LokiMetaSmith/NASA-COG/docs/references/datasheets/elec/ODECS/README.md

Reference documents for the ODECS.
Date 20231228
Version 1.1 Control and more!

AN_TF800.pdf is the application note on the Power Electronics TF800 series power supply

PowerSupply_SF_HDS800.pdf is the application note on the Power Electronics TF800 series power supply
