LokiMetaSmith/NASA-COG/docs/P_and_ID/Task 6 P_and_ID - Development Configuration rev_7_15_2024.png

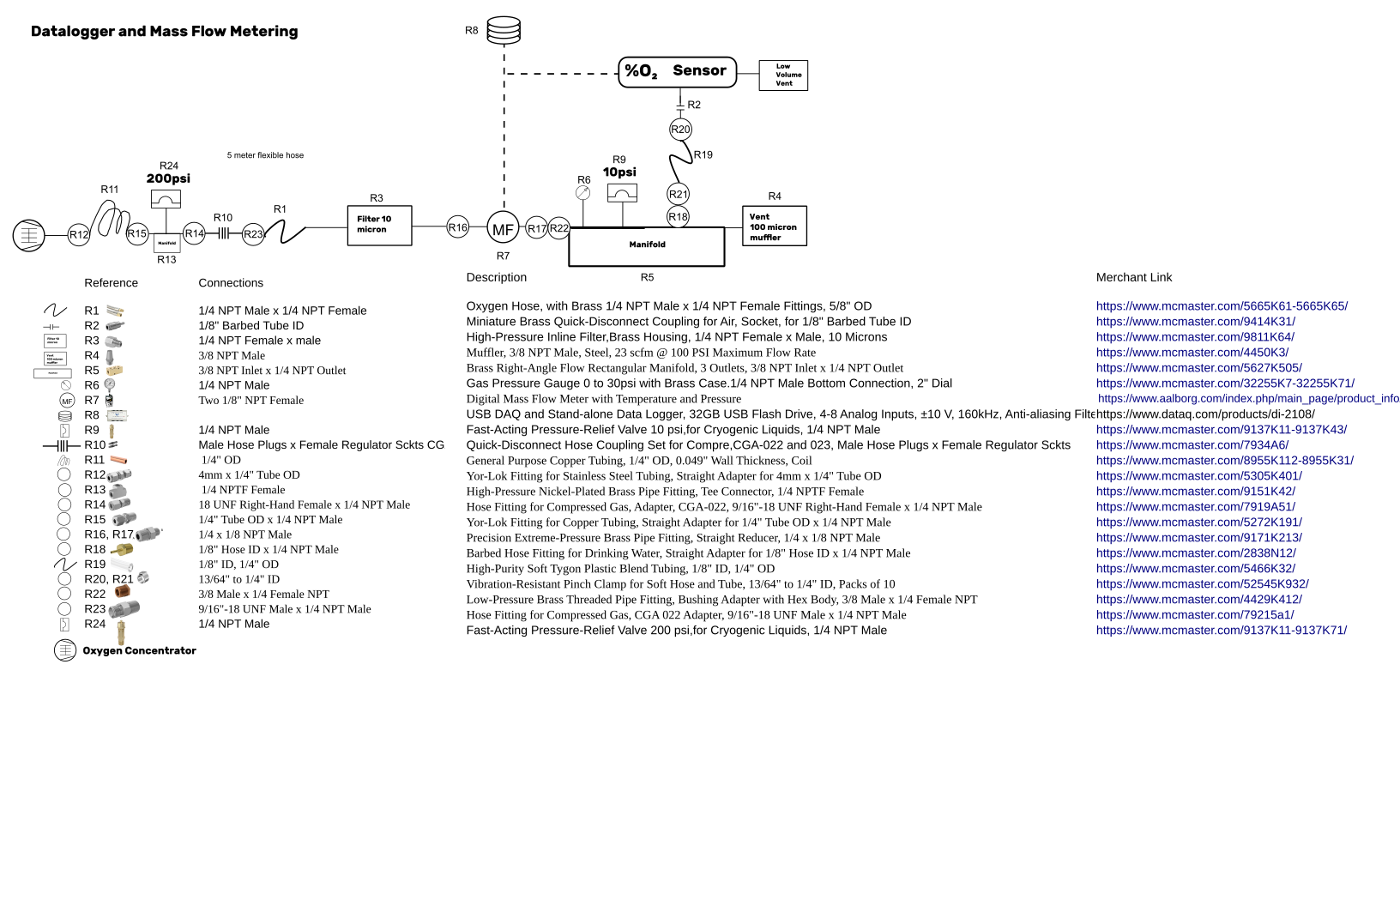
docs/P_and_ID/Task 6 P_and_ID - Development Configuration rev_7_15_2024.png
