LokiMetaSmith/NASA-COG/docs/Task6/Overalll System Diagram.png

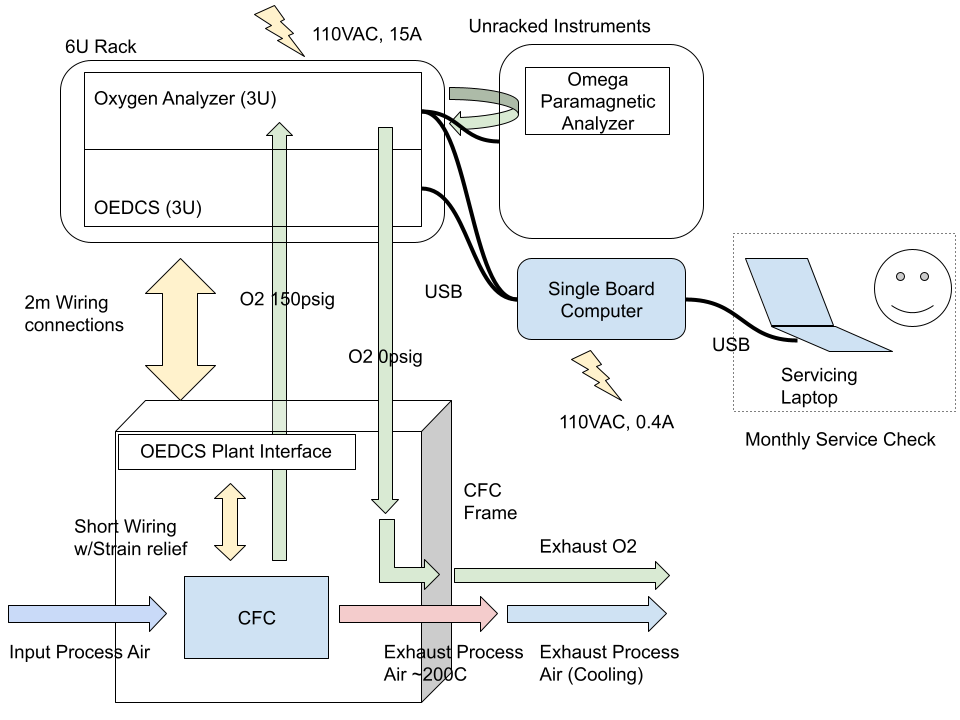
docs/Task6/Overalll System Diagram.png
