LokiMetaSmith/NASA-COG/elec/Control Board/Control_1v1/MountMini12864/20231210_202112.jpg

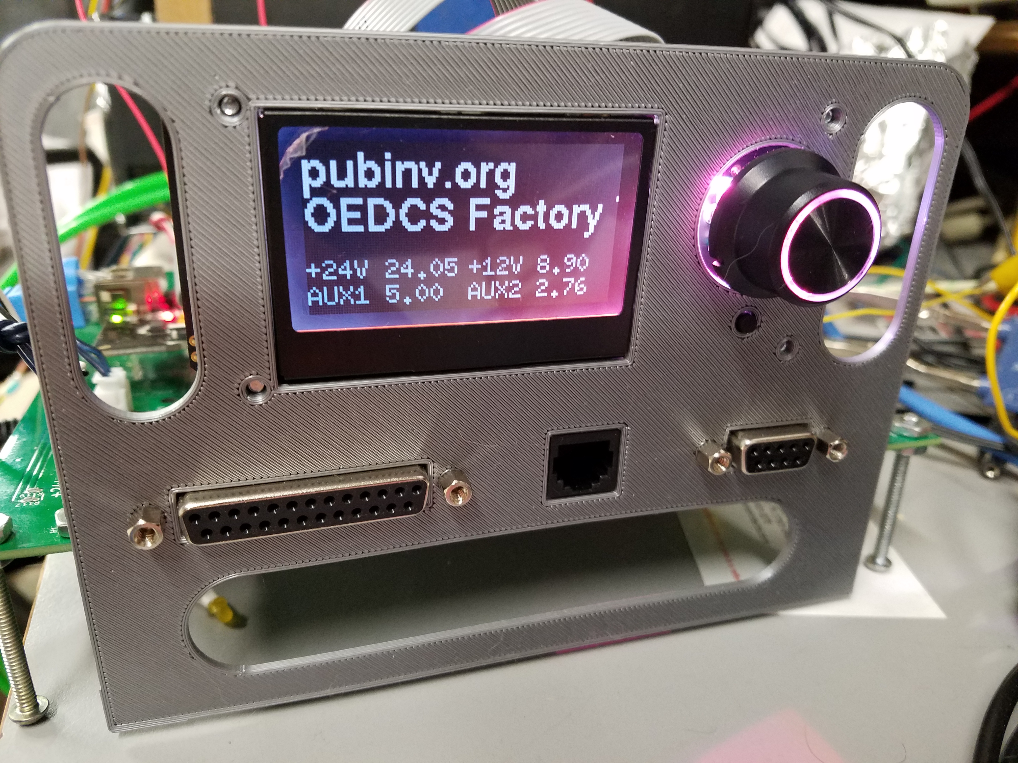
elec/Control Board/Control_1v1/MountMini12864/20231210_202112.jpg
