LokiMetaSmith/NASA-COG/elec/Control Board/Control_1v1/MountMini12864/BIGTREETECHMini12864Connector.png

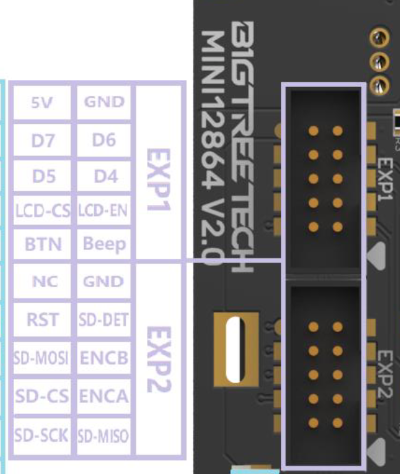
elec/Control Board/Control_1v1/MountMini12864/BIGTREETECHMini12864Connector.png
