LokiMetaSmith/NASA-COG/log-parser/Capture of various analysis views.PNG

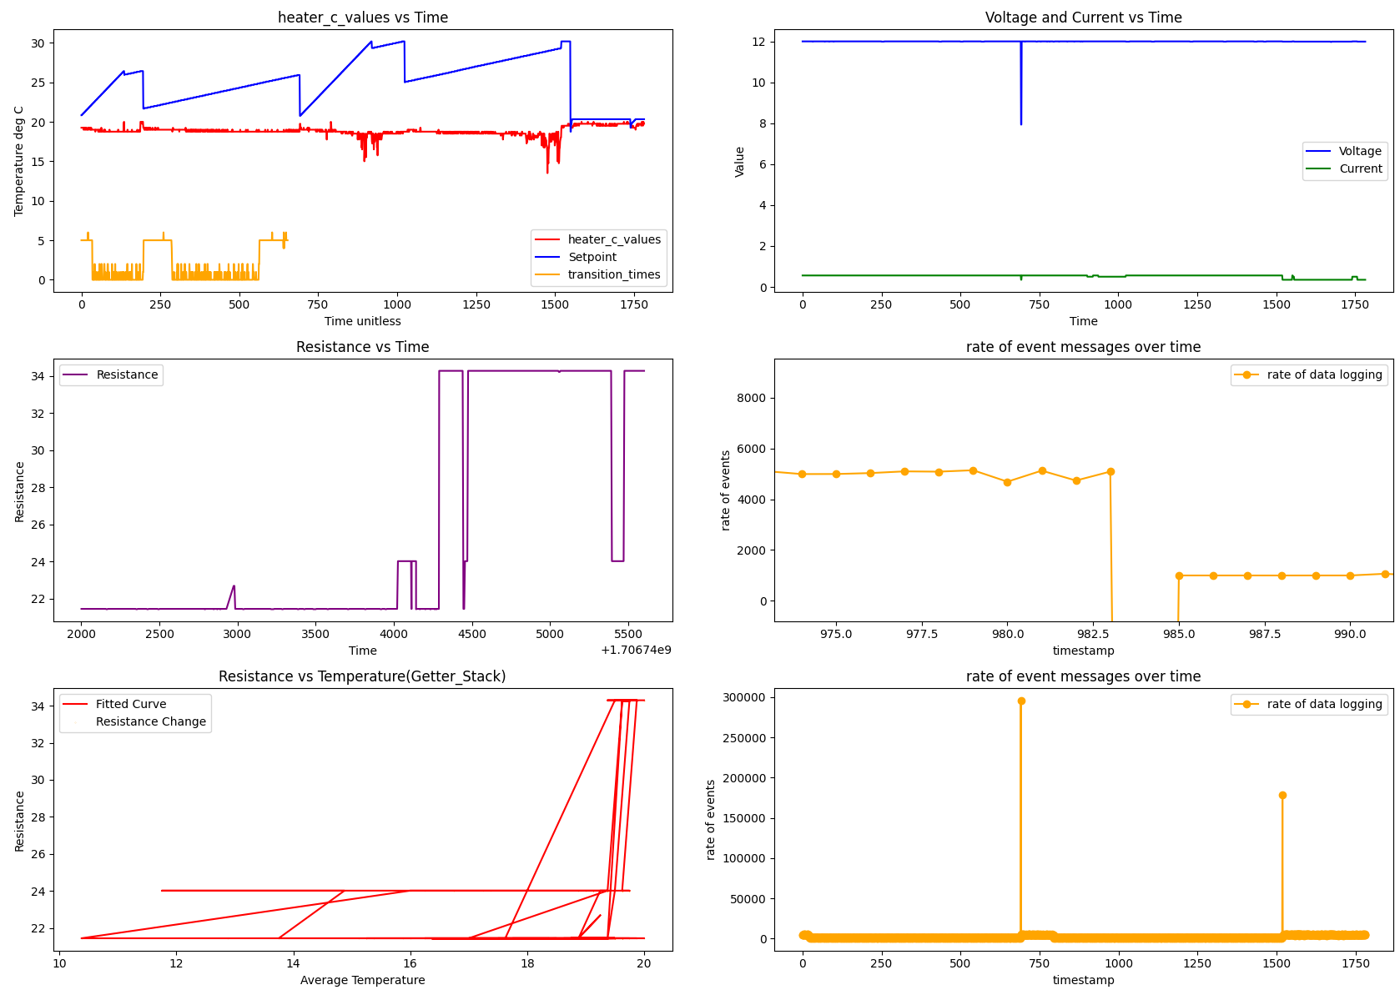
log-parser/Capture of various analysis views.PNG
