LokiMetaSmith/NASA-COG/log-parser/Rate of event messages in milliseconds.PNG

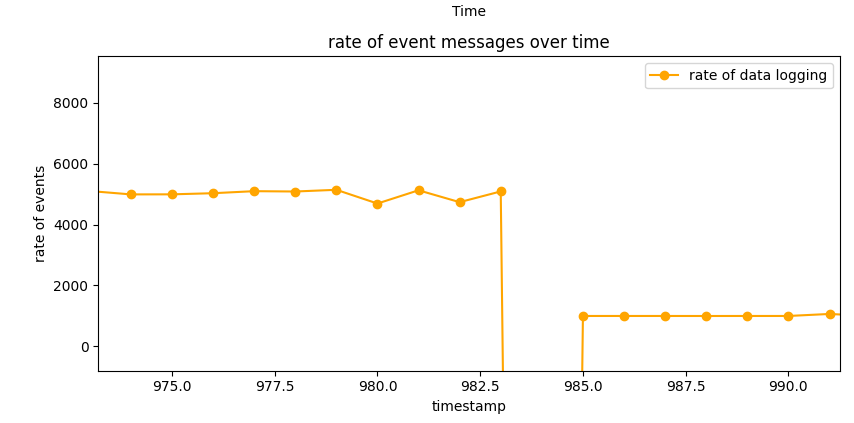
log-parser/Rate of event messages in milliseconds.PNG
