LokiMetaSmith/NASA-COG/elec/Control Board/Control_1v2/PL_Control_1v2_PLandPOS.xls

Sheet: RawImport_PL
Reference | Value | Footprint | Cost | Description | Distributor 1 | Distributor 1 PN | Qty
*_Designator | *_Comment101 | Footprint | 0 | Headers for JLCPCB BOM / PL | JLCPCB | JLCPCB Part # | 1
+3.3V101 | +3.3V | TestPoint:TestPoint_Loop_D2.54mm_Drill1.5mm_Beaded | 0.0696 | Test Points/Test Rings ROHS red | JLCPCB | C5277086 | 1
+5V101 | +5V | TestPoint:TestPoint_Loop_D2.54mm_Drill1.5mm_Beaded | 0.0696 | Test Points/Test Rings ROHS red | JLCPCB | C5277086 | 1
5VHead101 | 5VHead | TestPoint:TestPoint_Loop_D2.54mm_Drill1.5mm_Beaded | 0.0696 | Test Points/Test Rings ROHS red | JLCPCB | C5277086 | 1
C1 | 39pF | Capacitor_SMD:C_0603_1608Metric_Pad1.08x0.95mm_HandSolder | 0.003 | 50V 39pF NP0 Â±5% 0603 Multilayer Ceramic Ca | JLCPCB | C107049 | 1
C2 | 39pF | Capacitor_SMD:C_0603_1608Metric_Pad1.08x0.95mm_HandSolder | 0.003 | 50V 39pF NP0 Â±5% 0603 Multilayer Ceramic Ca | JLCPCB | C107049 | 1
C3 | 39pF | Capacitor_SMD:C_0603_1608Metric_Pad1.08x0.95mm_HandSolder | 0.003 | 50V 39pF NP0 Â±5% 0603 Multilayer Ceramic Ca | JLCPCB | C107049 | 1
C4 | 39pF | Capacitor_SMD:C_0603_1608Metric_Pad1.08x0.95mm_HandSolder | 0.003 | 50V 39pF NP0 Â±5% 0603 Multilayer Ceramic Ca | JLCPCB | C107049 | 1
C5 | 39pF | Capacitor_SMD:C_0603_1608Metric_Pad1.08x0.95mm_HandSolder | 0.003 | 50V 39pF NP0 Â±5% 0603 Multilayer Ceramic Ca | JLCPCB | C107049 | 1
C6 | 39pF | Capacitor_SMD:C_0603_1608Metric_Pad1.08x0.95mm_HandSolder | 0.003 | 50V 39pF NP0 Â±5% 0603 Multilayer Ceramic Ca | JLCPCB | C107049 | 1
C7 | 39pF | Capacitor_SMD:C_0603_1608Metric_Pad1.08x0.95mm_HandSolder | 0.003 | 50V 39pF NP0 Â±5% 0603 Multilayer Ceramic Ca | JLCPCB | C107049 | 1
C8 | 39pF | Capacitor_SMD:C_0603_1608Metric_Pad1.08x0.95mm_HandSolder | 0.003 | 50V 39pF NP0 Â±5% 0603 Multilayer Ceramic Ca | JLCPCB | C107049 | 1
C9 | 39pF | Capacitor_SMD:C_0603_1608Metric_Pad1.08x0.95mm_HandSolder | 0.003 | 50V 39pF NP0 Â±5% 0603 Multilayer Ceramic Ca | JLCPCB | C107049 | 1
C10 | 39pF | Capacitor_SMD:C_0603_1608Metric_Pad1.08x0.95mm_HandSolder | 0.003 | 50V 39pF NP0 Â±5% 0603 Multilayer Ceramic Ca | JLCPCB | C107049 | 1
C11 | 39pF | Capacitor_SMD:C_0603_1608Metric_Pad1.08x0.95mm_HandSolder | 0.003 | 50V 39pF NP0 Â±5% 0603 Multilayer Ceramic Ca | JLCPCB | C107049 | 1
C18 | 1uF | Capacitor_SMD:C_0603_1608Metric_Pad1.08x0.95mm_HandSolder | 0.0037 | 50V 1uF Â±5% 0603 Multilayer Ceramic Ca | JLCPCB | C91183 | 1
C19 | 1uF | Capacitor_SMD:C_0603_1608Metric_Pad1.08x0.95mm_HandSolder | 0.0037 | 50V 1uF Â±5% 0603 Multilayer Ceramic Ca | JLCPCB | C91183 | 1
C20 | 39pF | Capacitor_SMD:C_0603_1608Metric_Pad1.08x0.95mm_HandSolder | 0.003 | 50V 39pF NP0 Â±5% 0603 Multilayer Ceramic Ca | JLCPCB | C107049 | 1
C21 | 39pF | Capacitor_SMD:C_0603_1608Metric_Pad1.08x0.95mm_HandSolder | 0.003 | 50V 39pF NP0 Â±5% 0603 Multilayer Ceramic Ca | JLCPCB | C107049 | 1
C22 | 10nF | Capacitor_SMD:C_0603_1608Metric_Pad1.08x0.95mm_HandSolder | 0.0132 | 50V 10nF NP0 Â±5% 0603 Multilayer Ceramic Capacitors MLCC - SMD/SMT ROHS | JLCPCB | C389113 | 1
C23 | 39pF | Capacitor_SMD:C_0603_1608Metric_Pad1.08x0.95mm_HandSolder | 0.003 | 50V 39pF NP0 Â±5% 0603 Multilayer Ceramic Ca | JLCPCB | C107049 | 1
C24 | 1uF | Capacitor_SMD:C_0603_1608Metric_Pad1.08x0.95mm_HandSolder | 0.0037 | 50V 1uF Â±5% 0603 Multilayer Ceramic Ca | JLCPCB | C91183 | 1
D1 | 5.1V | Diode_SMD:D_MiniMELF | 0.0097 | Â±5% 500mW 5.1V MiniMELF(SOD-80) Zener Diodes ROHS | JLCPCB | C2857227 | 1
D2 | 5.1V | Diode_SMD:D_MiniMELF | 0.0097 | Â±5% 500mW 5.1V MiniMELF(SOD-80) Zener Diodes ROHS | JLCPCB | C2857227 | 1
D3 | 1N5819WS | Diode_SMD:D_SOD-323 | 0.0119 | 40V 600mV@1A 1A SOD-323 Schottky Barrier Diodes (SBD) ROHS | JLCPCB | C191023 | 1
D4 | RED 0603 | LED_SMD:LED_0603_1608Metric_Pad1.05x0.95mm_HandSolder | 0.0054 | LED RED CLEAR SMD | JLCPCB | C2286 | 1
D801 | 1N5819WS | Diode_SMD:D_SOD-323 | 0.0119 | 40V 600mV@1A 1A SOD-323 Schottky Barrier Diodes (SBD) ROHS | JLCPCB | C191023 | 1
D_PSU_RX1 | D_PSU_RX | TestPoint:TestPoint_Loop_D2.54mm_Drill1.5mm_Beaded | 0.0792 | Test Points/Test Rings ROHS black | JLCPCB | C5199807 | 1
D_PSU_RX2 | D_PSU_RX2 | TestPoint:TestPoint_Loop_D2.54mm_Drill1.5mm_Beaded | 0.0792 | Test Points/Test Rings ROHS black | JLCPCB | C5199807 | 1
D_PSU_TX1 | D_PSU_TX | TestPoint:TestPoint_Loop_D2.54mm_Drill1.5mm_Beaded | 0.1865 | Test Points/Test Rings ROHS white | JLCPCB | C5199812 | 1
D_PSU_TX2 | D_PSU_TX2 | TestPoint:TestPoint_Loop_D2.54mm_Drill1.5mm_Beaded | 0.1865 | Test Points/Test Rings ROHS white | JLCPCB | C5199812 | 1
F801 | Polyfuse_0603_1A | Fuse:Fuse_0603_1608Metric | 0.2448 | 6V 1A 50A -40â„ƒ~+85â„ƒ 1.8A 40mÎ© 300ms 120mÎ© 0603 Resettable Fuses ROHS | JLCPCB | C207017 | 1
J1 | DB9_Female_MountingHoles | Connector_Dsub:DSUB-9_Female_Horizontal_P2.77x2.84mm_EdgePinOffset4.94mm_Housed_MountingHolesOffset7.48mm | 0.2718 | 9P Female D-Sub Shrouded 2 3A -50â„ƒ~+105â„ƒ Plugin D-Sub/DVI/HDMI Connectors ROHS | JLCPCB | C141882 | 1
J2 | Conn_01x08 | Connector_PinSocket_2.54mm:PinSocket_1x08_P2.54mm_Vertical | 0.0762 | 2.54mm Plugin 3A 8P -40â„ƒ~+105â„ƒ Straight 1x8P 8.5mm Top Square Holes Plugin,P=2.54mm Female Headers ROHS | JLCPCB | C2905417 | 1
J3 | Conn_01x08 | Connector_PinSocket_2.54mm:PinSocket_1x08_P2.54mm_Vertical | 0.0762 | 2.54mm Plugin 3A 8P -40â„ƒ~+105â„ƒ Straight 1x8P 8.5mm Top Square Holes Plugin,P=2.54mm Female Headers ROHS | JLCPCB | C2905417 | 1
J4 | Conn_01x08 | Connector_PinSocket_2.54mm:PinSocket_1x08_P2.54mm_Vertical | 0.0762 | 2.54mm Plugin 3A 8P -40â„ƒ~+105â„ƒ Straight 1x8P 8.5mm Top Square Holes Plugin,P=2.54mm Female Headers ROHS | JLCPCB | C2905417 | 1
J5 | Conn_01x08 | Connector_PinSocket_2.54mm:PinSocket_1x08_P2.54mm_Vertical | 0.0762 | 2.54mm Plugin 3A 8P -40â„ƒ~+105â„ƒ Straight 1x8P 8.5mm Top Square Holes Plugin,P=2.54mm Female Headers ROHS | JLCPCB | C2905417 | 1
J6 | Conn_01x08 | Connector_PinSocket_2.54mm:PinSocket_1x08_P2.54mm_Vertical | 0.0762 | 2.54mm Plugin 3A 8P -40â„ƒ~+105â„ƒ Straight 1x8P 8.5mm Top Square Holes Plugin,P=2.54mm Female Headers ROHS | JLCPCB | C2905417 | 1
J7 | Conn_01x10 | Connector_PinSocket_2.54mm:PinSocket_1x10_P2.54mm_Vertical | 0.0942 | 2.54mm Plugin 3A 10P -40â„ƒ~+105â„ƒ Straight 1x10P 8.5mm Top Square Holes Plugin,P=2.54mm Female Headers ROHS | JLCPCB | C2905418 | 1
J8 | Conn_02x18_Odd_Even | Connector_PinSocket_2.54mm:PinSocket_2x18_P2.54mm_Vertical | 0.3441 | 2.54mm 2.54mm åŒæŽ’ 36P Straight 2x18P Plugin,P=2.54mm Female Headers ROHS | JLCPCB | C132131 | 1
J9 | Conn_01x10 | Connector_PinSocket_2.54mm:PinSocket_1x10_P2.54mm_Vertical | 0.0942 | 2.54mm Plugin 3A 10P -40â„ƒ~+105â„ƒ Straight 1x10P 8.5mm Top Square Holes Plugin,P=2.54mm Female Headers ROHS | JLCPCB | C2905418 | 1
J10 | Conn_02x12_Odd_Even | PubInv_KiCad_PCB:JST_PHD_B24B-PHDSS_2x12_P2.00mm_Vertical | 1000000 | Conn_02x12_Odd_Even | JLCPCB | C160327 | 1
J11 | Con_01x02_2.5mm | PubInv_KiCad_PCB:JST_XH_B2B-XH-AM_1x02_P2.50mm_Vertical | 0.2156 | 1x2P 2P XH Gold 2 -25â„ƒ~+85â„ƒ 3A 1 2.5mm Brass Direct Insert Plugin,P=2.5mm Wire To Board Connector ROHS | JLCPCB | C265283 | 1
J12 | Con_01x02_2.5mm | PubInv_KiCad_PCB:JST_XH_B2B-XH-AM_1x02_P2.50mm_Vertical | 0.2156 | 1x2P 2P XH Gold 2 -25â„ƒ~+85â„ƒ 3A 1 2.5mm Brass Direct Insert Plugin,P=2.5mm Wire To Board Connector ROHS | JLCPCB | C265283 | 1
J13 | Con_01x02_2.5mm | PubInv_KiCad_PCB:JST_XH_B2B-XH-AM_1x02_P2.50mm_Vertical | 0.2156 | 1x2P 2P XH Gold 2 -25â„ƒ~+85â„ƒ 3A 1 2.5mm Brass Direct Insert Plugin,P=2.5mm Wire To Board Connector ROHS | JLCPCB | C265283 | 1
J14 | Conn_01x10 | Connector_PinSocket_2.54mm:PinSocket_1x10_P2.54mm_Vertical | 0.0942 | 2.54mm Plugin 3A 10P -40â„ƒ~+105â„ƒ Straight 1x10P 8.5mm Top Square Holes Plugin,P=2.54mm Female Headers ROHS | JLCPCB | C2905418 | 1
J15 | DB25_Female_MountingHoles | Connector_Dsub:DSUB-25_Female_Horizontal_P2.77x2.84mm_EdgePinOffset4.94mm_Housed_MountingHolesOffset7.48mm | 0.7217 | 25P Female D-Sub Shrouded 2 3A -50â„ƒ~+105â„ƒ Plugin D-Sub/DVI/HDMI Connectors ROHS | JLCPCB | C190083 | 1
J16 | Conn_01x04 | Connector_PinHeader_2.54mm:PinHeader_1x04_P2.54mm_Vertical | 0.0342 | 2.54mm Plugin 3A 4P -40â„ƒ~+105â„ƒ Straight 1x4P 8.5mm Top Square Holes Plugin,P=2.54mm Female Headers ROHS | JLCPCB | C6332197 | 1
J17 | Conn_01x05 | Connector_PinHeader_2.54mm:PinHeader_1x05_P2.54mm_Vertical | 0.0791 | 2.54mm Plugin 3A 5P -40â„ƒ~+105â„ƒ Straight 1x5P 8.5mm Top Square Holes Plugin,P=2.54mm Female Headers ROHS | JLCPCB | C2897368 | 1
J18 | Conn_01x04 | Connector_PinHeader_2.54mm:PinHeader_1x04_P2.54mm_Vertical | 0.0342 | 2.54mm Plugin 3A 4P -40â„ƒ~+105â„ƒ Straight 1x4P 8.5mm Top Square Holes Plugin,P=2.54mm Female Headers ROHS | JLCPCB | C6332197 | 1
J19 | Conn_01x07 | Connector_PinHeader_2.54mm:PinHeader_1x07_P2.54mm_Vertical | 0.0543 | 2.54mm Plugin 3A 7P -40â„ƒ~+105â„ƒ Straight 1x7P 8.5mm Top Square Holes Plugin,P=2.54mm Female Headers ROHS | JLCPCB | C2932672 | 1
J23 | Con_01x02_0.1" | Connector_PinHeader_2.54mm:PinHeader_1x02_P2.54mm_Vertical | 0.0115 | Direct Insert Policy 2.5mm 2P 6mm -40â„ƒ~+105â„ƒ 3mm 2.54mm Single Row Black Brass 1x2P Plugin,P=2.54mm Pin Headers ROHS | JLCPCB | C492401 | 1
J24 | Conn_01x04 | Connector_PinHeader_2.54mm:PinHeader_1x04_P2.54mm_Vertical | 0.0342 | 2.54mm Plugin 3A 4P -40â„ƒ~+105â„ƒ Straight 1x4P 8.5mm Top Square Holes Plugin,P=2.54mm Female Headers ROHS | JLCPCB | C6332197 | 1
J25 | Con_01x02_2.5mm | PubInv_KiCad_PCB:JST_XH_B2B-XH-AM_1x02_P2.50mm_Vertical | 0.2156 | 1x2P 2P XH Gold 2 -25â„ƒ~+85â„ƒ 3A 1 2.5mm Brass Direct Insert Plugin,P=2.5mm Wire To Board Connector ROHS | JLCPCB | C265283 | 1
J26 | Conn_01x10 | Connector_PinSocket_2.54mm:PinSocket_1x10_P2.54mm_Vertical | 0.0942 | 2.54mm Plugin 3A 10P -40â„ƒ~+105â„ƒ Straight 1x10P 8.5mm Top Square Holes Plugin,P=2.54mm Female Headers ROHS | JLCPCB | C2905418 | 1
J27 | Conn_02x12_Odd_Even | PubInv_KiCad_PCB:JST_PHD_B24B-PHDSS_2x12_P2.00mm_Vertical | 1000000 | Conn_02x12_Odd_Even | JLCPCB | C160327 | 1
J28 | Con_01x02_2.5mm | PubInv_KiCad_PCB:JST_XH_B2B-XH-AM_1x02_P2.50mm_Vertical | 0.2156 | 1x2P 2P XH Gold 2 -25â„ƒ~+85â„ƒ 3A 1 2.5mm Brass Direct Insert Plugin,P=2.5mm Wire To Board Connector ROHS | JLCPCB | C265283 | 1
J29 | Conn_01x10 | Connector_PinSocket_2.54mm:PinSocket_1x10_P2.54mm_Vertical | 0.0942 | 2.54mm Plugin 3A 10P -40â„ƒ~+105â„ƒ Straight 1x10P 8.5mm Top Square Holes Plugin,P=2.54mm Female Headers ROHS | JLCPCB | C2905418 | 1
J30 | Con_01x02_2.5mm | PubInv_KiCad_PCB:JST_XH_B2B-XH-AM_1x02_P2.50mm_Vertical | 0.2156 | 1x2P 2P XH Gold 2 -25â„ƒ~+85â„ƒ 3A 1 2.5mm Brass Direct Insert Plugin,P=2.5mm Wire To Board Connector ROHS | JLCPCB | C265283 | 1
J31 | Con_01x02_2.5mm | PubInv_KiCad_PCB:JST_XH_B2B-XH-AM_1x02_P2.50mm_Vertical | 0.2156 | 1x2P 2P XH Gold 2 -25â„ƒ~+85â„ƒ 3A 1 2.5mm Brass Direct Insert Plugin,P=2.5mm Wire To Board Connector ROHS | JLCPCB | C265283 | 1
J32 | Con_01x02_2.5mm | PubInv_KiCad_PCB:JST_XH_B2B-XH-AM_1x02_P2.50mm_Vertical | 0.2156 | 1x2P 2P XH Gold 2 -25â„ƒ~+85â„ƒ 3A 1 2.5mm Brass Direct Insert Plugin,P=2.5mm Wire To Board Connector ROHS | JLCPCB | C265283 | 1
J33 | Con_01x02_2.5mm | PubInv_KiCad_PCB:JST_XH_B2B-XH-AM_1x02_P2.50mm_Vertical | 0.2156 | 1x2P 2P XH Gold 2 -25â„ƒ~+85â„ƒ 3A 1 2.5mm Brass Direct Insert Plugin,P=2.5mm Wire To Board Connector ROHS | JLCPCB | C265283 | 1
J34 | Con_01x02_2.5mm | PubInv_KiCad_PCB:JST_XH_B2B-XH-AM_1x02_P2.50mm_Vertical | 0.2156 | 1x2P 2P XH Gold 2 -25â„ƒ~+85â„ƒ 3A 1 2.5mm Brass Direct Insert Plugin,P=2.5mm Wire To Board Connector ROHS | JLCPCB | C265283 | 1
J35 | Conn_02x05_Odd_Even | Connector_IDC:IDC-Header_2x05_P2.54mm_Vertical | 0.48 | 2.54mm Box 10Pin Male Straight | JLCPCB | C5665 | 1
J36 | Conn_02x05_Odd_Even | Connector_IDC:IDC-Header_2x05_P2.54mm_Vertical | 0.48 | 2.54mm Box 10Pin Male Straight | JLCPCB | C5665 | 1
J37 | Conn_01x04 | Connector_PinHeader_2.54mm:PinHeader_1x04_P2.54mm_Vertical | 0.0342 | 2.54mm Plugin 3A 4P -40â„ƒ~+105â„ƒ Straight 1x4P 8.5mm Top Square Holes Plugin,P=2.54mm Female Headers ROHS | JLCPCB | C6332197 | 1
J101 | Con_01x02_2.5mm | PubInv_KiCad_PCB:JST_XH_B2B-XH-AM_1x02_P2.50mm_Vertical | 0.2156 | 1x2P 2P XH Gold 2 -25â„ƒ~+85â„ƒ 3A 1 2.5mm Brass Direct Insert Plugin,P=2.5mm Wire To Board Connector ROHS | JLCPCB | C265283 | 1
J201 | Con_01x02_2.5mm | PubInv_KiCad_PCB:JST_XH_B2B-XH-AM_1x02_P2.50mm_Vertical | 0.2156 | 1x2P 2P XH Gold 2 -25â„ƒ~+85â„ƒ 3A 1 2.5mm Brass Direct Insert Plugin,P=2.5mm Wire To Board Connector ROHS | JLCPCB | C265283 | 1
J801 | Conn_01x03_0.1" | Connector_PinHeader_2.54mm:PinHeader_1x03_P2.54mm_Vertical | 0.0141 | Gold 250V 3A Direct Insert Policy 2.54mm 3P 260â„ƒ 6mm -40â„ƒ~+105â„ƒ 3mm 2.54mm Brass Black Single Row 2.54mm 1x3P Plugin,P=2.54mm Pin Headers ROHS | JLCPCB | C6332196 | 1
J802 | Con_01x02_0.1" | Connector_PinHeader_2.54mm:PinHeader_1x02_P2.54mm_Vertical | 0.0115 | Direct Insert Policy 2.5mm 2P 6mm -40â„ƒ~+105â„ƒ 3mm 2.54mm Single Row Black Brass 1x2P Plugin,P=2.54mm Pin Headers ROHS | JLCPCB | C492401 | 1
J804 | Screw_Terminal_01x02_5.08mm | TerminalBlock_Phoenix:TerminalBlock_Phoenix_MKDS-1,5-2-5.08_1x02_P5.08mm_Horizontal | 0.1551 | Screw_Terminal_01x02_5.08mm | JLCPCB | C5142622 | 1
J805 | Con_01x02_0.1" | Connector_PinHeader_2.54mm:PinHeader_1x02_P2.54mm_Vertical | 0.0115 | Direct Insert Policy 2.5mm 2P 6mm -40â„ƒ~+105â„ƒ 3mm 2.54mm Single Row Black Brass 1x2P Plugin,P=2.54mm Pin Headers ROHS | JLCPCB | C492401 | 1
JP9 | MAX31850K | PubInv_KiCad_PCB:Adafruit_MAX31850K_Module | 14.95 | 2.54mm Plugin 3A 8P -40â„ƒ~+105â„ƒ Straight 1x8P 8.5mm Top Square Holes Plugin,P=2.54mm Female Headers ROHS | JLCPCB | C2905417 | 1
JP10 | MAX31850K | PubInv_KiCad_PCB:Adafruit_MAX31850K_Module | 14.95 | 2.54mm Plugin 3A 8P -40â„ƒ~+105â„ƒ Straight 1x8P 8.5mm Top Square Holes Plugin,P=2.54mm Female Headers ROHS | JLCPCB | C2905417 | 1
JP15 | MAX31850K | PubInv_KiCad_PCB:Adafruit_MAX31850K_Module | 14.95 | 2.54mm Plugin 3A 8P -40â„ƒ~+105â„ƒ Straight 1x8P 8.5mm Top Square Holes Plugin,P=2.54mm Female Headers ROHS | JLCPCB | C2905417 | 1
JP16 | MAX31855 | PubInv_KiCad_PCB:Adafruit_MAX31855_Module | 14.95 | 2.54mm Plugin 3A 6P -40â„ƒ~+105â„ƒ Straight 1x6P 8.5mm Top Square Holes Plugin,P=2.54mm Female Headers ROHS | JLCPCB | C2905416 | 1
JP17 | MAX31855 | PubInv_KiCad_PCB:Adafruit_MAX31855_Module | 14.95 | 2.54mm Plugin 3A 6P -40â„ƒ~+105â„ƒ Straight 1x6P 8.5mm Top Square Holes Plugin,P=2.54mm Female Headers ROHS | JLCPCB | C2905416 | 1
JP18 | MAX31855 | PubInv_KiCad_PCB:Adafruit_MAX31855_Module | 14.95 | 2.54mm Plugin 3A 6P -40â„ƒ~+105â„ƒ Straight 1x6P 8.5mm Top Square Holes Plugin,P=2.54mm Female Headers ROHS | JLCPCB | C2905416 | 1
JP19 | MCP9600 | PubInv_KiCad_PCB:Adafruit_MCP9600_Module | 15.95 | 2.54mm Plugin 3A 9P -40â„ƒ~+105â„ƒ Straight 1x9P 8.5mm Top Square Holes Plugin,P=2.54mm Female Headers ROHS | JLCPCB | C2932673 | 1
JP20 | MCP9600 | PubInv_KiCad_PCB:Adafruit_MCP9600_Module | 15.95 | 2.54mm Plugin 3A 9P -40â„ƒ~+105â„ƒ Straight 1x9P 8.5mm Top Square Holes Plugin,P=2.54mm Female Headers ROHS | JLCPCB | C2932673 | 1
JP21 | MCP9600 | PubInv_KiCad_PCB:Adafruit_MCP9600_Module | 15.95 | 2.54mm Plugin 3A 9P -40â„ƒ~+105â„ƒ Straight 1x9P 8.5mm Top Square Holes Plugin,P=2.54mm Female Headers ROHS | JLCPCB | C2932673 | 1
JP205 | MAX31850K | PubInv_KiCad_PCB:Adafruit_MAX31850K_Module | 14.95 | 2.54mm Plugin 3A 8P -40â„ƒ~+105â„ƒ Straight 1x8P 8.5mm Top Square Holes Plugin,P=2.54mm Female Headers ROHS | JLCPCB | C2905417 | 1
K801 | Relay SRU-12VDC | Relay_THT:Relay_SPDT_Omron-G5LE-1 | 0.4224 | Relay SRU-12VDC-SL-C | JLCPCB | C47402 | 1
Q1 | BSS138 | Package_TO_SOT_SMD:SOT-23 | 0.0196 | 50V 220mA 3.5Î©@10V,220mA 360mW 1.5V@1mA N Channel SOT-23 MOSFETs ROHS | JLCPCB | C400505 | 1
Q2 | NCE01P30K | Package_TO_SOT_SMD:TO-252-2 | $0.51 | P Channel -100V 30A(Tc) 2.5V @ 250uA 58mÎ© @ 15A,10V 120W(Tc) TO-252-2L MOSFET RoHS | JLCPCB | C115991 | 1
Q3 | BSS138 | Package_TO_SOT_SMD:SOT-23 | 0.0196 | 50V 220mA 3.5Î©@10V,220mA 360mW 1.5V@1mA N Channel SOT-23 MOSFETs ROHS | JLCPCB | C400505 | 1
Q4 | BSS138 | Package_TO_SOT_SMD:SOT-23 | 0.0196 | 50V 220mA 3.5Î©@10V,220mA 360mW 1.5V@1mA N Channel SOT-23 MOSFETs ROHS | JLCPCB | C400505 | 1
Q9 | BSS138 | Package_TO_SOT_SMD:SOT-23 | 0.0196 | 50V 220mA 3.5Î©@10V,220mA 360mW 1.5V@1mA N Channel SOT-23 MOSFETs ROHS | JLCPCB | C400505 | 1
Q10 | BSS138 | Package_TO_SOT_SMD:SOT-23 | 0.0196 | 50V 220mA 3.5Î©@10V,220mA 360mW 1.5V@1mA N Channel SOT-23 MOSFETs ROHS | JLCPCB | C400505 | 1
Q11 | BSS138 | Package_TO_SOT_SMD:SOT-23 | 0.0196 | 50V 220mA 3.5Î©@10V,220mA 360mW 1.5V@1mA N Channel SOT-23 MOSFETs ROHS | JLCPCB | C400505 | 1
Q12 | BSS138 | Package_TO_SOT_SMD:SOT-23 | 0.0196 | 50V 220mA 3.5Î©@10V,220mA 360mW 1.5V@1mA N Channel SOT-23 MOSFETs ROHS | JLCPCB | C400505 | 1
Q13 | BSS138 | Package_TO_SOT_SMD:SOT-23 | 0.0196 | 50V 220mA 3.5Î©@10V,220mA 360mW 1.5V@1mA N Channel SOT-23 MOSFETs ROHS | JLCPCB | C400505 | 1
Q14 | BSS138 | Package_TO_SOT_SMD:SOT-23 | 0.0196 | 50V 220mA 3.5Î©@10V,220mA 360mW 1.5V@1mA N Channel SOT-23 MOSFETs ROHS | JLCPCB | C400505 | 1
Q801 | BSS138 | Package_TO_SOT_SMD:SOT-23 | 0.0196 | 50V 220mA 3.5Î©@10V,220mA 360mW 1.5V@1mA N Channel SOT-23 MOSFETs ROHS | JLCPCB | C400505 | 1
R1 | 1R0 | Resistor_SMD:R_0603_1608Metric_Pad0.98x0.95mm_HandSolder | 0.0015 | 0.1W Â±5% 1Î© 0603 Chip Resistor - Surface Mount ROHS | JLCPCB | C269434 | 1
R2 | 1R0 | Resistor_SMD:R_0603_1608Metric_Pad0.98x0.95mm_HandSolder | 0.0015 | 0.1W Â±5% 1Î© 0603 Chip Resistor - Surface Mount ROHS | JLCPCB | C269434 | 1
R3 | 1R0 | Resistor_SMD:R_0603_1608Metric_Pad0.98x0.95mm_HandSolder | 0.0015 | 0.1W Â±5% 1Î© 0603 Chip Resistor - Surface Mount ROHS | JLCPCB | C269434 | 1
R4 | 1R0 | Resistor_SMD:R_0603_1608Metric_Pad0.98x0.95mm_HandSolder | 0.0015 | 0.1W Â±5% 1Î© 0603 Chip Resistor - Surface Mount ROHS | JLCPCB | C269434 | 1
R5 | 1R0 | Resistor_SMD:R_0603_1608Metric_Pad0.98x0.95mm_HandSolder | 0.0015 | 0.1W Â±5% 1Î© 0603 Chip Resistor - Surface Mount ROHS | JLCPCB | C269434 | 1
R6 | 1R0 | Resistor_SMD:R_0603_1608Metric_Pad0.98x0.95mm_HandSolder | 0.0015 | 0.1W Â±5% 1Î© 0603 Chip Resistor - Surface Mount ROHS | JLCPCB | C269434 | 1
R7 | 1R0 | Resistor_SMD:R_0603_1608Metric_Pad0.98x0.95mm_HandSolder | 0.0015 | 0.1W Â±5% 1Î© 0603 Chip Resistor - Surface Mount ROHS | JLCPCB | C269434 | 1
R8 | 1R0 | Resistor_SMD:R_0603_1608Metric_Pad0.98x0.95mm_HandSolder | 0.0015 | 0.1W Â±5% 1Î© 0603 Chip Resistor - Surface Mount ROHS | JLCPCB | C269434 | 1
R9 | 1R0 | Resistor_SMD:R_0603_1608Metric_Pad0.98x0.95mm_HandSolder | 0.0015 | 0.1W Â±5% 1Î© 0603 Chip Resistor - Surface Mount ROHS | JLCPCB | C269434 | 1
R10 | 1R0 | Resistor_SMD:R_0603_1608Metric_Pad0.98x0.95mm_HandSolder | 0.0015 | 0.1W Â±5% 1Î© 0603 Chip Resistor - Surface Mount ROHS | JLCPCB | C269434 | 1
R11 | 1R0 | Resistor_SMD:R_0603_1608Metric_Pad0.98x0.95mm_HandSolder | 0.0015 | 0.1W Â±5% 1Î© 0603 Chip Resistor - Surface Mount ROHS | JLCPCB | C269434 | 1
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
R81 | 10K | Resistor_SMD:R_0603_1608Metric_Pad0.98x0.95mm_HandSolder | 0.0015 | 100mW Â±1% 10kÎ© 0603 Chip Resistor - Surface Mount ROHS | JLCPCB | C269701 | 1
R82 | 1R0 | Resistor_SMD:R_0603_1608Metric_Pad0.98x0.95mm_HandSolder | 0.0015 | 0.1W Â±5% 1Î© 0603 Chip Resistor - Surface Mount ROHS | JLCPCB | C269434 | 1
R83 | 4K7 | Resistor_SMD:R_0603_1608Metric_Pad0.98x0.95mm_HandSolder | 0.0015 | 100mW Thick Film Resistors Â±100ppm/â„ƒ Â±1% 4.7kÎ© 0603 Chip Resistor - Surface Mount ROHS | JLCPCB | C23162 | 1
R84 | 1R0 | Resistor_SMD:R_0603_1608Metric_Pad0.98x0.95mm_HandSolder | 0.0015 | 0.1W Â±5% 1Î© 0603 Chip Resistor - Surface Mount ROHS | JLCPCB | C269434 | 1
R88 | 1R0 | Resistor_SMD:R_0603_1608Metric_Pad0.98x0.95mm_HandSolder | 0.0015 | 0.1W Â±5% 1Î© 0603 Chip Resistor - Surface Mount ROHS | JLCPCB | C269434 | 1
R91 | 1R0 | Resistor_SMD:R_0603_1608Metric_Pad0.98x0.95mm_HandSolder | 0.0015 | 0.1W Â±5% 1Î© 0603 Chip Resistor - Surface Mount ROHS | JLCPCB | C269434 | 1
R92 | 1R0 | Resistor_SMD:R_0603_1608Metric_Pad0.98x0.95mm_HandSolder | 0.0015 | 0.1W Â±5% 1Î© 0603 Chip Resistor - Surface Mount ROHS | JLCPCB | C269434 | 1
R97 | 1R0 | Resistor_SMD:R_0603_1608Metric_Pad0.98x0.95mm_HandSolder | 0.0015 | 0.1W Â±5% 1Î© 0603 Chip Resistor - Surface Mount ROHS | JLCPCB | C269434 | 1
R98 | 1R0 | Resistor_SMD:R_0603_1608Metric_Pad0.98x0.95mm_HandSolder | 0.0015 | 0.1W Â±5% 1Î© 0603 Chip Resistor - Surface Mount ROHS | JLCPCB | C269434 | 1
R99 | 1R0 | Resistor_SMD:R_0603_1608Metric_Pad0.98x0.95mm_HandSolder | 0.0015 | 0.1W Â±5% 1Î© 0603 Chip Resistor - Surface Mount ROHS | JLCPCB | C269434 | 1
R100 | 1K | Resistor_SMD:R_0603_1608Metric_Pad0.98x0.95mm_HandSolder | 0.0015 | 0.1W Â±1% 1kÎ© 0603 Chip Resistor - Surface Mount ROHS | JLCPCB | C269704 | 1
R101 | 10K | Resistor_SMD:R_0603_1608Metric_Pad0.98x0.95mm_HandSolder | 0.0015 | 100mW Â±1% 10kÎ© 0603 Chip Resistor - Surface Mount ROHS | JLCPCB | C269701 | 1
R102 | 4K7 | Resistor_SMD:R_0603_1608Metric_Pad0.98x0.95mm_HandSolder | 0.0015 | 100mW Thick Film Resistors Â±100ppm/â„ƒ Â±1% 4.7kÎ© 0603 Chip Resistor - Surface Mount ROHS | JLCPCB | C23162 | 1
R103 | 10K | Resistor_SMD:R_0603_1608Metric_Pad0.98x0.95mm_HandSolder | 0.0015 | 100mW Â±1% 10kÎ© 0603 Chip Resistor - Surface Mount ROHS | JLCPCB | C269701 | 1
R104 | 10K | Resistor_SMD:R_0603_1608Metric_Pad0.98x0.95mm_HandSolder | 0.0015 | 100mW Â±1% 10kÎ© 0603 Chip Resistor - Surface Mount ROHS | JLCPCB | C269701 | 1
R105 | 10K | Resistor_SMD:R_0603_1608Metric_Pad0.98x0.95mm_HandSolder | 0.0015 | 100mW Â±1% 10kÎ© 0603 Chip Resistor - Surface Mount ROHS | JLCPCB | C269701 | 1
R106 | 20K | Resistor_SMD:R_0603_1608Metric_Pad0.98x0.95mm_HandSolder | 0.0008 | 100mW Thick Film Resistors 75V Â±100ppm/â„ƒ Â±1% 10kÎ© 0603 Chip Resistor - Surface Mount ROHS | JLCPCB | C25804 | 1
R107 | 10K | Resistor_SMD:R_0603_1608Metric_Pad0.98x0.95mm_HandSolder | 0.0015 | 100mW Â±1% 10kÎ© 0603 Chip Resistor - Surface Mount ROHS | JLCPCB | C269701 | 1
R108 | 20K | Resistor_SMD:R_0603_1608Metric_Pad0.98x0.95mm_HandSolder | 0.0008 | 100mW Thick Film Resistors 75V Â±100ppm/â„ƒ Â±1% 10kÎ© 0603 Chip Resistor - Surface Mount ROHS | JLCPCB | C25804 | 1
R109 | 1R0 | Resistor_SMD:R_0603_1608Metric_Pad0.98x0.95mm_HandSolder | 0.0015 | 0.1W Â±5% 1Î© 0603 Chip Resistor - Surface Mount ROHS | JLCPCB | C269434 | 1
R110 | 1R0 | Resistor_SMD:R_0603_1608Metric_Pad0.98x0.95mm_HandSolder | 0.0015 | 0.1W Â±5% 1Î© 0603 Chip Resistor - Surface Mount ROHS | JLCPCB | C269434 | 1
R111 | 1R0 | Resistor_SMD:R_0603_1608Metric_Pad0.98x0.95mm_HandSolder | 0.0015 | 0.1W Â±5% 1Î© 0603 Chip Resistor - Surface Mount ROHS | JLCPCB | C269434 | 1
R112 | 1R0 | Resistor_SMD:R_0603_1608Metric_Pad0.98x0.95mm_HandSolder | 0.0015 | 0.1W Â±5% 1Î© 0603 Chip Resistor - Surface Mount ROHS | JLCPCB | C269434 | 1
R113 | 10K | Resistor_SMD:R_0603_1608Metric_Pad0.98x0.95mm_HandSolder | 0.0015 | 100mW Â±1% 10kÎ© 0603 Chip Resistor - Surface Mount ROHS | JLCPCB | C269701 | 1
R114 | 10K | Resistor_SMD:R_0603_1608Metric_Pad0.98x0.95mm_HandSolder | 0.0015 | 100mW Â±1% 10kÎ© 0603 Chip Resistor - Surface Mount ROHS | JLCPCB | C269701 | 1
R115 | 1K | Resistor_SMD:R_0603_1608Metric_Pad0.98x0.95mm_HandSolder | 0.0015 | 0.1W Â±1% 1kÎ© 0603 Chip Resistor - Surface Mount ROHS | JLCPCB | C269704 | 1
R116 | 1K | Resistor_SMD:R_0603_1608Metric_Pad0.98x0.95mm_HandSolder | 0.0015 | 0.1W Â±1% 1kÎ© 0603 Chip Resistor - Surface Mount ROHS | JLCPCB | C269704 | 1
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
R181 | 4K7 | Resistor_SMD:R_0603_1608Metric_Pad0.98x0.95mm_HandSolder | 0.0015 | 100mW Thick Film Resistors Â±100ppm/â„ƒ Â±1% 4.7kÎ© 0603 Chip Resistor - Surface Mount ROHS | JLCPCB | C23162 | 1
R182 | 10K | Resistor_SMD:R_0603_1608Metric_Pad0.98x0.95mm_HandSolder | 0.0015 | 100mW Â±1% 10kÎ© 0603 Chip Resistor - Surface Mount ROHS | JLCPCB | C269701 | 1
R183 | 10K | Resistor_SMD:R_0603_1608Metric_Pad0.98x0.95mm_HandSolder | 0.0015 | 100mW Â±1% 10kÎ© 0603 Chip Resistor - Surface Mount ROHS | JLCPCB | C269701 | 1
R184 | 2K | Resistor_SMD:R_0603_1608Metric_Pad0.98x0.95mm_HandSolder | 0.0015 | 100mW Â±1% 2kÎ© 0603 Chip Resistor - Surface Mount ROHS | JLCPCB | C269421 | 1
R185 | 2K | Resistor_SMD:R_0603_1608Metric_Pad0.98x0.95mm_HandSolder | 0.0015 | 100mW Â±1% 2kÎ© 0603 Chip Resistor - Surface Mount ROHS | JLCPCB | C269421 | 1
R201 | 1K | Resistor_SMD:R_0603_1608Metric_Pad0.98x0.95mm_HandSolder | 0.0015 | 0.1W Â±1% 1kÎ© 0603 Chip Resistor - Surface Mount ROHS | JLCPCB | C269704 | 1
R202 | 1K | Resistor_SMD:R_0603_1608Metric_Pad0.98x0.95mm_HandSolder | 0.0015 | 0.1W Â±1% 1kÎ© 0603 Chip Resistor - Surface Mount ROHS | JLCPCB | C269704 | 1
R203 | 1K | Resistor_SMD:R_0603_1608Metric_Pad0.98x0.95mm_HandSolder | 0.0015 | 0.1W Â±1% 1kÎ© 0603 Chip Resistor - Surface Mount ROHS | JLCPCB | C269704 | 1
R204 | 1K | Resistor_SMD:R_0603_1608Metric_Pad0.98x0.95mm_HandSolder | 0.0015 | 0.1W Â±1% 1kÎ© 0603 Chip Resistor - Surface Mount ROHS | JLCPCB | C269704 | 1
R801 | 1R0 | Resistor_SMD:R_0603_1608Metric_Pad0.98x0.95mm_HandSolder | 0.0015 | 0.1W Â±5% 1Î© 0603 Chip Resistor - Surface Mount ROHS | JLCPCB | C269434 | 1
R802 | 10K | Resistor_SMD:R_0603_1608Metric_Pad0.98x0.95mm_HandSolder | 0.0015 | 100mW Â±1% 10kÎ© 0603 Chip Resistor - Surface Mount ROHS | JLCPCB | C269701 | 1
R803 | 1K | Resistor_SMD:R_0603_1608Metric_Pad0.98x0.95mm_HandSolder | 0.0015 | 0.1W Â±1% 1kÎ© 0603 Chip Resistor - Surface Mount ROHS | JLCPCB | C269704 | 1
R804 | 1R0 | Resistor_SMD:R_0603_1608Metric_Pad0.98x0.95mm_HandSolder | 0.0015 | 0.1W Â±5% 1Î© 0603 Chip Resistor - Surface Mount ROHS | JLCPCB | C269434 | 1
R806 | 1R0 | Resistor_SMD:R_0603_1608Metric_Pad0.98x0.95mm_HandSolder | 0.0015 | 0.1W Â±5% 1Î© 0603 Chip Resistor - Surface Mount ROHS | JLCPCB | C269434 | 1
R807 | 1R0 | Resistor_SMD:R_0603_1608Metric_Pad0.98x0.95mm_HandSolder | 0.0015 | 0.1W Â±5% 1Î© 0603 Chip Resistor - Surface Mount ROHS | JLCPCB | C269434 | 1
S1 | SWITCH_TACTILE_SPST-NO_0.05A_24V | PubInv_KiCad_PCB:Switch_Tactile_THT_6x6mm | 0.0315 | Â±10% Â±100ppm/â„ƒ 10kÎ© Plugin Variable Resistors/Potentiometers ROHS | JLCPCB | C428628 | 1
S2 | SWITCH_TACTILE_SPST-NO_0.05A_24V | PubInv_KiCad_PCB:Switch_Tactile_THT_6x6mm | 0.0315 | Â±10% Â±100ppm/â„ƒ 10kÎ© Plugin Variable Resistors/Potentiometers ROHS | JLCPCB | C428628 | 1
TP1 | GND | TestPoint:TestPoint_Loop_D2.54mm_Drill1.5mm_Beaded | 0.1865 | Test Points/Test Rings ROHS green | JLCPCB | C7589090 | 1
TP2 | +12V | TestPoint:TestPoint_Loop_D2.54mm_Drill1.5mm_Beaded | 0.0696 | Test Points/Test Rings ROHS red | JLCPCB | C5277086 | 1
TP3 | GND | TestPoint:TestPoint_Loop_D2.54mm_Drill1.5mm_Beaded | 0.1865 | Test Points/Test Rings ROHS green | JLCPCB | C7589090 | 1
TP4 | GND | TestPoint:TestPoint_Loop_D2.54mm_Drill1.5mm_Beaded | 0.1865 | Test Points/Test Rings ROHS green | JLCPCB | C7589090 | 1
TP5 | +VccMAX31850 | TestPoint:TestPoint_Loop_D2.54mm_Drill1.5mm_Beaded | 0.0696 | Test Points/Test Rings ROHS red | JLCPCB | C5277086 | 1
TP6 | +VccMAX31850_1 | TestPoint:TestPoint_Loop_D2.54mm_Drill1.5mm_Beaded | 0.0696 | Test Points/Test Rings ROHS red | JLCPCB | C5277086 | 1
TP7 | +VccMAX31850_2 | TestPoint:TestPoint_Loop_D2.54mm_Drill1.5mm_Beaded | 0.0696 | Test Points/Test Rings ROHS red | JLCPCB | C5277086 | 1
TP8 | +VccMAX31850_3 | TestPoint:TestPoint_Loop_D2.54mm_Drill1.5mm_Beaded | 0.0696 | Test Points/Test Rings ROHS red | JLCPCB | C5277086 | 1
TP9 | +VccMAX3185 | TestPoint:TestPoint_Loop_D2.54mm_Drill1.5mm_Beaded | 0.0696 | Test Points/Test Rings ROHS red | JLCPCB | C5277086 | 1
TP10 | +VccMCP9600 | TestPoint:TestPoint_Loop_D2.54mm_Drill1.5mm_Beaded | 0.0696 | Test Points/Test Rings ROHS red | JLCPCB | C5277086 | 1
TP11 | GND | TestPoint:TestPoint_Loop_D2.54mm_Drill1.5mm_Beaded | 0.1865 | Test Points/Test Rings ROHS green | JLCPCB | C7589090 | 1
TP17 | I2C_VCC | TestPoint:TestPoint_Loop_D2.54mm_Drill1.5mm_Beaded | 0.0696 | Test Points/Test Rings ROHS red | JLCPCB | C5277086 | 1
TP18 | SCL_5V | TestPoint:TestPoint_Loop_D2.54mm_Drill1.5mm_Beaded | 0.0696 | Test Points/Test Rings ROHS red | JLCPCB | C5277086 | 1
TP19 | SDA_5V | TestPoint:TestPoint_Loop_D2.54mm_Drill1.5mm_Beaded | 0.0696 | Test Points/Test Rings ROHS red | JLCPCB | C5277086 | 1
TP20 | +24V | TestPoint:TestPoint_Loop_D2.54mm_Drill1.5mm_Beaded | 0.0696 | Test Points/Test Rings ROHS red | JLCPCB | C5277086 | 1
TP21 | GND | TestPoint:TestPoint_Loop_D2.54mm_Drill1.5mm_Beaded | 0.1865 | Test Points/Test Rings ROHS green | JLCPCB | C7589090 | 1
TP201 | +VccMAX31850_3 | TestPoint:TestPoint_Loop_D2.54mm_Drill1.5mm_Beaded | 0.0696 | Test Points/Test Rings ROHS red | JLCPCB | C5277086 | 1
TP999 | TestPoint | TestPoint:TestPoint_Loop_D2.54mm_Drill1.5mm_Beaded | 0.0696 | Test Points/Test Rings ROHS red | JLCPCB | C5277086 | 1
TPSwitched_Fan_Power1 | Switched_Fan_Power | TestPoint:TestPoint_Loop_D2.54mm_Drill1.5mm_Beaded | 0.0696 | Test Points/Test Rings ROHS red | JLCPCB | C5277086 | 1
TP_CIPO1 | CIPO | TestPoint:TestPoint_Loop_D2.54mm_Drill1.5mm_Beaded | 0.0714 | Test Points/Test Rings ROHS yellow | JLCPCB | C5199804 | 1
TP_COPI1 | COPI | TestPoint:TestPoint_Loop_D2.54mm_Drill1.5mm_Beaded | 0.0714 | Test Points/Test Rings ROHS yellow | JLCPCB | C5199804 | 1
TP_SCL1 | SCL | TestPoint:TestPoint_Loop_D2.54mm_Drill1.5mm_Beaded | 0.0714 | Test Points/Test Rings ROHS yellow | JLCPCB | C5199804 | 1
TP_SCL2 | SCL1 | TestPoint:TestPoint_Loop_D2.54mm_Drill1.5mm_Beaded | 0.0714 | Test Points/Test Rings ROHS yellow | JLCPCB | C5199804 | 1
TP_SDA1 | SDA | TestPoint:TestPoint_Loop_D2.54mm_Drill1.5mm_Beaded | 0.0714 | Test Points/Test Rings ROHS yellow | JLCPCB | C5199804 | 1
TP_SDA2 | SDA1 | TestPoint:TestPoint_Loop_D2.54mm_Drill1.5mm_Beaded | 0.0714 | Test Points/Test Rings ROHS yellow | JLCPCB | C5199804 | 1
TP_SD_DET1 | TP_SD_DET | TestPoint:TestPoint_Loop_D2.54mm_Drill1.5mm_Beaded | 0.0714 | Test Points/Test Rings ROHS yellow | JLCPCB | C5199804 | 1
TP_SPI_SCK1 | SPI_SCK | TestPoint:TestPoint_Loop_D2.54mm_Drill1.5mm_Beaded | 0.0714 | Test Points/Test Rings ROHS yellow | JLCPCB | C5199804 | 1
TP_VIN1 | VIN1 | TestPoint:TestPoint_Loop_D2.54mm_Drill1.5mm_Beaded | 0.0696 | Test Points/Test Rings ROHS red | JLCPCB | C5277086 | 1

Sheet: RawImport_POS
Ref | Val | Package | PosX | PosY | Rot | Side
+3.3V101 | +3.3V | TestPoint_Loop_D2.54mm_Drill1.5mm_Beaded | 92.403 | -124.622 | 0 | top
+5V101 | +5V | TestPoint_Loop_D2.54mm_Drill1.5mm_Beaded | 93.165 | -93.38 | 0 | top
5VHead101 | 5VHead | TestPoint_Loop_D2.54mm_Drill1.5mm_Beaded | 167.079 | -185.328 | 0 | top
A1 | Arduino Due with Headers | Arduino_Due_Shield_Annotated | 108.38 | -50.48 | -90 | top
C1 | 39pF | C_0603_1608Metric_Pad1.08x0.95mm_HandSolder | 63.1 | -182 | -90 | top
C2 | 39pF | C_0603_1608Metric_Pad1.08x0.95mm_HandSolder | 63.75 | -168.75 | 180 | top
C3 | 39pF | C_0603_1608Metric_Pad1.08x0.95mm_HandSolder | 64.1375 | -86.75 | 180 | top
C4 | 39pF | C_0603_1608Metric_Pad1.08x0.95mm_HandSolder | 64 | -82 | 0 | top
C5 | 39pF | C_0603_1608Metric_Pad1.08x0.95mm_HandSolder | 64.1375 | -89.8 | 180 | top
C6 | 39pF | C_0603_1608Metric_Pad1.08x0.95mm_HandSolder | 63.9375 | -92.4 | 180 | top
C7 | 39pF | C_0603_1608Metric_Pad1.08x0.95mm_HandSolder | 63.9375 | -95.2 | 180 | top
C8 | 39pF | C_0603_1608Metric_Pad1.08x0.95mm_HandSolder | 63.9375 | -107 | 180 | top
C9 | 39pF | C_0603_1608Metric_Pad1.08x0.95mm_HandSolder | 64.5 | -103.75 | 180 | top
C10 | 39pF | C_0603_1608Metric_Pad1.08x0.95mm_HandSolder | 64.1375 | -100.6 | 180 | top
C11 | 39pF | C_0603_1608Metric_Pad1.08x0.95mm_HandSolder | 64.1375 | -98 | 180 | top
C18 | 1uF | C_0603_1608Metric_Pad1.08x0.95mm_HandSolder | 75.8625 | -162.5 | 180 | top
C19 | 1uF | C_0603_1608Metric_Pad1.08x0.95mm_HandSolder | 67.86875 | -174.5 | 90 | top
C20 | 39pF | C_0603_1608Metric_Pad1.08x0.95mm_HandSolder | 63 | -178 | 90 | top
C21 | 39pF | C_0603_1608Metric_Pad1.08x0.95mm_HandSolder | 63 | -174 | -90 | top
C22 | 10nF | C_0603_1608Metric_Pad1.08x0.95mm_HandSolder | 179.017 | -38.77 | -90 | top
C23 | 39pF | C_0603_1608Metric_Pad1.08x0.95mm_HandSolder | 93 | -65.5 | 180 | top
C24 | 1uF | C_0603_1608Metric_Pad1.08x0.95mm_HandSolder | 116.279 | -168.056 | 0 | top
D1 | 5.1V | D_MiniMELF | 75 | -113 | 0 | top
D2 | 5.1V | D_MiniMELF | 74.19 | -92.5 | 0 | top
D3 | 1N5819WS | D_SOD-323 | 101.75 | -82.25 | 90 | top
D4 | RED 0603 | LED_0603_1608Metric_Pad1.05x0.95mm_HandSolder | 170.25 | -75.5 | 0 | top
D801 | 1N5819WS | D_SOD-323 | 215.339 | -174.66 | 90 | top
D_PSU_RX1 | D_PSU_RX | TestPoint_Loop_D2.54mm_Drill1.5mm_Beaded | 166 | -141.3 | 0 | top
D_PSU_RX2 | D_PSU_RX2 | TestPoint_Loop_D2.54mm_Drill1.5mm_Beaded | 183.843 | -123.352 | 0 | top
D_PSU_TX1 | D_PSU_TX | TestPoint_Loop_D2.54mm_Drill1.5mm_Beaded | 171.25 | -141.25 | 0 | top
D_PSU_TX2 | D_PSU_TX2 | TestPoint_Loop_D2.54mm_Drill1.5mm_Beaded | 176.731 | -122.25 | 0 | top
F801 | Polyfuse_0603_1A | Fuse_0603_1608Metric | 216.6345 | -187.868 | 180 | top
J10 | Conn_02x12_Odd_Even | JST_PHD_B24B-PHDSS_2x12_P2.00mm_Vertical | 177.493 | -184.566 | 90 | top
J11 | Con_01x02_2.5mm | JST_XH_B2B-XH-AM_1x02_P2.50mm_Vertical | 101.73 | -55 | 0 | top
J12 | Con_01x02_2.5mm | JST_XH_B2B-XH-AM_1x02_P2.50mm_Vertical | 70.23 | -55 | 0 | top
J13 | Con_01x02_2.5mm | JST_XH_B2B-XH-AM_1x02_P2.50mm_Vertical | 80 | -55 | 0 | top
J20 | Conn_01x04_KK-254_0470531000 | Molex_KK-254_0470531000_1x04_P2.54mm_Vertical_ForFAN | 67.511 | -122.082 | 90 | top
J23 | Con_01x02_0.1 | PinHeader_1x02_P2.54mm_Vertical | 66.46 | -156 | 90 | top
J24 | Conn_01x04 | PinHeader_1x04_P2.54mm_Vertical | 53.38 | -157 | 90 | top
J25 | Con_01x02_2.5mm | JST_XH_B2B-XH-AM_1x02_P2.50mm_Vertical | 183.5 | -190 | -90 | top
J28 | Con_01x02_2.5mm | JST_XH_B2B-XH-AM_1x02_P2.50mm_Vertical | 182.59 | -115.752 | -90 | top
J30 | Con_01x02_2.5mm | JST_XH_B2B-XH-AM_1x02_P2.50mm_Vertical | 182.0875 | -77.23 | -90 | top
J31 | Con_01x02_2.5mm | JST_XH_B2B-XH-AM_1x02_P2.50mm_Vertical | 182 | -65.71 | -90 | top
J32 | Con_01x02_2.5mm | JST_XH_B2B-XH-AM_1x02_P2.50mm_Vertical | 178.235 | -217.603 | 180 | top
J33 | Con_01x02_2.5mm | JST_XH_B2B-XH-AM_1x02_P2.50mm_Vertical | 169.599 | -217.603 | 180 | top
J34 | Con_01x02_2.5mm | JST_XH_B2B-XH-AM_1x02_P2.50mm_Vertical | 75.893 | -217.84 | 180 | top
J37 | Conn_01x04 | PinHeader_1x04_P2.54mm_Vertical | 165.7855 | -47.152 | 0 | top
J201 | Con_01x02_2.5mm | JST_XH_B2B-XH-AM_1x02_P2.50mm_Vertical | 221.669 | -219.635 | 180 | top
J801 | Conn_01x03_0.1 | PinHeader_1x03_P2.54mm_Vertical | 142.441 | -168.31 | 0 | top
J802 | Con_01x02_0.1 | PinHeader_1x02_P2.54mm_Vertical | 148.029 | -172.12 | 0 | top
J804 | Screw_Terminal_01x02_5.08mm | TerminalBlock_Phoenix_MKDS-1,5-2-5.08_1x02_P5.08mm_Horizontal | 224.991 | -193.456 | 90 | top
J805 | Con_01x02_0.1 | PinHeader_1x03_P2.54mm_Vertical | 152.679 | 172.12 | 0 | top
JP9 | MAX31850K | Adafruit_MAX31850K_Module | 155 | -193.95 | 180 | top
JP10 | MAX31850K | Adafruit_MAX31850K_Module | 127.725 | -193.95 | 180 | top
JP15 | MAX31850K | Adafruit_MAX31850K_Module | 100.28 | -193.95 | 180 | top
JP205 | MAX31850K | Adafruit_MAX31850K_Module | 213.546 | -204.04448 | 180 | top
K801 | Relay SRU-12VDC | Relay_SPDT_Omron-G5LE-1 | 211.275 | -179.74 | -90 | top
Q1 | BSS138 | SOT-23 | 78.4375 | -116 | 180 | top
Q2 | NCE01P30K | TO-252-2 | 71.5 | -73.565 | -90 | top
Q3 | BSS138 | SOT-23 | 78.5 | -71 | 180 | top
Q4 | BSS138 | SOT-23 | 76.25 | -61.25 | 180 | top
Q9 | BSS138 | SOT-23 | 70.55 | -187.85 | -90 | top
Q10 | BSS138 | SOT-23 | 70.4625 | -171.39375 | -90 | top
Q11 | BSS138 | SOT-23 | 176.3375 | -76.5 | 0 | top
Q12 | BSS138 | SOT-23 | 176.25 | -65 | 0 | top
Q13 | BSS138 | SOT-23 | 170 | -175.5 | 90 | top
Q14 | BSS138 | SOT-23 | 152.093 | -101 | 90 | top
Q801 | BSS138 | SOT-23 | 194.511 | -190.8375 | 90 | top
R1 | 1R0 | R_0603_1608Metric_Pad0.98x0.95mm_HandSolder | 105.992 | -188.376 | -90 | top
R2 | 1R0 | R_0603_1608Metric_Pad0.98x0.95mm_HandSolder | 159.5 | -191.95 | -90 | top
R3 | 1R0 | R_0603_1608Metric_Pad0.98x0.95mm_HandSolder | 129.5 | -187.394 | -90 | top
R4 | 1R0 | R_0603_1608Metric_Pad0.98x0.95mm_HandSolder | 156.5 | -188.3625 | -90 | top
R5 | 1R0 | R_0603_1608Metric_Pad0.98x0.95mm_HandSolder | 83.5 | -176.5 | -90 | top
R6 | 1R0 | R_0603_1608Metric_Pad0.98x0.95mm_HandSolder | 86.5 | -176.5 | -90 | top
R7 | 1R0 | R_0603_1608Metric_Pad0.98x0.95mm_HandSolder | 134 | -186.344 | -90 | top
R8 | 1R0 | R_0603_1608Metric_Pad0.98x0.95mm_HandSolder | 64 | -167 | 0 | top
R9 | 1R0 | R_0603_1608Metric_Pad0.98x0.95mm_HandSolder | 80.5 | -63.5 | 180 | top
R10 | 1R0 | R_0603_1608Metric_Pad0.98x0.95mm_HandSolder | 82.9125 | -75.25 | 0 | top
R11 | 1R0 | R_0603_1608Metric_Pad0.98x0.95mm_HandSolder | 86.25 | -121.75 | 0 | top
R12 | 1R0 | R_0603_1608Metric_Pad0.98x0.95mm_HandSolder | 79 | -120 | 0 | top
R13 | 1R0 | R_0603_1608Metric_Pad0.98x0.95mm_HandSolder | 164.5 | -148 | 90 | top
R14 | 1K | R_0603_1608Metric_Pad0.98x0.95mm_HandSolder | 171.5 | -148 | -90 | top
R15 | 1R0 | R_0603_1608Metric_Pad0.98x0.95mm_HandSolder | 173.5 | -148 | -90 | top
R16 | 1R0 | R_0603_1608Metric_Pad0.98x0.95mm_HandSolder | 167 | -148 | -90 | top
R17 | DNI | R_0603_1608Metric_Pad0.98x0.95mm_HandSolder | 154 | -179.5 | -90 | top
R18 | 1K | R_0603_1608Metric_Pad0.98x0.95mm_HandSolder | 153 | -188.25 | -90 | top
R19 | 1K | R_0603_1608Metric_Pad0.98x0.95mm_HandSolder | 150 | -188.25 | -90 | top
R20 | 1K | R_0603_1608Metric_Pad0.98x0.95mm_HandSolder | 147 | -188.2 | -90 | top
R21 | 1K | R_0603_1608Metric_Pad0.98x0.95mm_HandSolder | 125.16 | -188.175 | -90 | top
R22 | 1K | R_0603_1608Metric_Pad0.98x0.95mm_HandSolder | 144 | -188.2 | -90 | top
R23 | 1K | R_0603_1608Metric_Pad0.98x0.95mm_HandSolder | 122.65 | -188.175 | -90 | top
R24 | 1K | R_0603_1608Metric_Pad0.98x0.95mm_HandSolder | 120.14 | -188.175 | -90 | top
R25 | 1K | R_0603_1608Metric_Pad0.98x0.95mm_HandSolder | 117.295 | -188.175 | -90 | top
R26 | 1K | R_0603_1608Metric_Pad0.98x0.95mm_HandSolder | 98.5 | -189.12302 | -90 | top
R27 | 1K | R_0603_1608Metric_Pad0.98x0.95mm_HandSolder | 95.5 | -189.12302 | -90 | top
R28 | 1K | R_0603_1608Metric_Pad0.98x0.95mm_HandSolder | 92.5 | -189.12302 | -90 | top
R29 | 1K | R_0603_1608Metric_Pad0.98x0.95mm_HandSolder | 89.47 | -189.21052 | -90 | top
R30 | DNI | R_0603_1608Metric_Pad0.98x0.95mm_HandSolder | 131.5 | -187.394 | -90 | top
R31 | 1R0 | R_0603_1608Metric_Pad0.98x0.95mm_HandSolder | 160 | -196.45 | -90 | top
R32 | 4M7 | R_0603_1608Metric_Pad0.98x0.95mm_HandSolder | 175.517 | -38.77 | -90 | top
R33 | 1R0 | R_0603_1608Metric_Pad0.98x0.95mm_HandSolder | 69.5 | -108.5 | 0 | top
R34 | DNI | R_0603_1608Metric_Pad0.98x0.95mm_HandSolder | 74.275 | -119.55 | 180 | top
R35 | DNI | R_0603_1608Metric_Pad0.98x0.95mm_HandSolder | 74.5 | -122.5 | 180 | top
R36 | 1K | R_0603_1608Metric_Pad0.98x0.95mm_HandSolder | 74.1625 | -116.75 | 0 | top
R37 | 1K | R_0603_1608Metric_Pad0.98x0.95mm_HandSolder | 78.25 | -124.25 | 0 | top
R38 | 1K | R_0603_1608Metric_Pad0.98x0.95mm_HandSolder | 81.5625 | -115.95 | 90 | top
R39 | 10K | R_0603_1608Metric_Pad0.98x0.95mm_HandSolder | 69.525 | -65.5 | 0 | top
R40 | 10K | R_0603_1608Metric_Pad0.98x0.95mm_HandSolder | 78 | -67.5 | 0 | top
R41 | 10K | R_0603_1608Metric_Pad0.98x0.95mm_HandSolder | 82 | -121.75 | 180 | top
R42 | 1K | R_0603_1608Metric_Pad0.98x0.95mm_HandSolder | 82 | -125 | 180 | top
R43 | DNI | R_0603_1608Metric_Pad0.98x0.95mm_HandSolder | 86.25 | -125 | 0 | top
R44 | 10K | R_0603_1608Metric_Pad0.98x0.95mm_HandSolder | 73.525 | -65.5 | 0 | top
R45 | 1K | R_0603_1608Metric_Pad0.98x0.95mm_HandSolder | 82.9125 | -72 | 0 | top
R46 | 10K | R_0603_1608Metric_Pad0.98x0.95mm_HandSolder | 83 | -69 | 180 | top
R47 | 1K | R_0603_1608Metric_Pad0.98x0.95mm_HandSolder | 80.5 | -60.5 | 180 | top
R48 | 1R0 | R_0603_1608Metric_Pad0.98x0.95mm_HandSolder | 71.5 | -60.5 | 180 | top
R66 | 1R0 | R_0603_1608Metric_Pad0.98x0.95mm_HandSolder | 79.5 | -162.5 | 180 | top
R67 | 10K | R_0603_1608Metric_Pad0.98x0.95mm_HandSolder | 70.4125 | -183.9125 | 180 | top
R68 | 10K | R_0603_1608Metric_Pad0.98x0.95mm_HandSolder | 70.4125 | -167.45625 | 180 | top
R69 | 10K | R_0603_1608Metric_Pad0.98x0.95mm_HandSolder | 69.7 | -191.8125 | 0 | top
R70 | 10K | R_0603_1608Metric_Pad0.98x0.95mm_HandSolder | 70.4125 | -175.45625 | 0 | top
R71 | 39R | R_0603_1608Metric_Pad0.98x0.95mm_HandSolder | 69.7 | -194.8125 | 0 | top
R72 | 39R | R_0603_1608Metric_Pad0.98x0.95mm_HandSolder | 70.5 | -178.45625 | 0 | top
R73 | 1R0 | R_0603_1608Metric_Pad0.98x0.95mm_HandSolder | 60.51 | -153.0875 | -90 | top
R74 | DNI | R_0603_1608Metric_Pad0.98x0.95mm_HandSolder | 58 | -153.0875 | -90 | top
R75 | DNI | R_0603_1608Metric_Pad0.98x0.95mm_HandSolder | 68 | -160 | 0 | top
R76 | 1R0 | R_0603_1608Metric_Pad0.98x0.95mm_HandSolder | 97.5 | -61 | -90 | top
R77 | 4K7 | R_0603_1608Metric_Pad0.98x0.95mm_HandSolder | 92.5 | -154.0875 | 90 | top
R78 | 4K7 | R_0603_1608Metric_Pad0.98x0.95mm_HandSolder | 89 | -154.0875 | 90 | top
R79 | 1R0 | R_0603_1608Metric_Pad0.98x0.95mm_HandSolder | 175 | -189.75 | 90 | top
R80 | 1R0 | R_0603_1608Metric_Pad0.98x0.95mm_HandSolder | 178.25 | -189.75 | 90 | top
R81 | 10K | R_0603_1608Metric_Pad0.98x0.95mm_HandSolder | 84.5 | -60.5 | 0 | top
R82 | 1R0 | R_0603_1608Metric_Pad0.98x0.95mm_HandSolder | 161 | -187.95 | 90 | top
R83 | 4K7 | R_0603_1608Metric_Pad0.98x0.95mm_HandSolder | 101.5 | -188.95 | 90 | top
R84 | 1R0 | R_0603_1608Metric_Pad0.98x0.95mm_HandSolder | 160 | -201 | -90 | top
R85 | DNI | R_0603_1608Metric_Pad0.98x0.95mm_HandSolder | 134.5 | -189.95 | -90 | top
R86 | DNI | R_0603_1608Metric_Pad0.98x0.95mm_HandSolder | 108.5 | -188.45 | -90 | top
R87 | DNI | R_0603_1608Metric_Pad0.98x0.95mm_HandSolder | 82.5 | -188.95 | -90 | top
R88 | 1R0 | R_0603_1608Metric_Pad0.98x0.95mm_HandSolder | 67.5 | -61.5 | 0 | top
R89 | DNI | R_0603_1608Metric_Pad0.98x0.95mm_HandSolder | 84.5 | -64.5 | 180 | top
R90 | DNI | R_0603_1608Metric_Pad0.98x0.95mm_HandSolder | 66 | -77.5 | 0 | top
R91 | 1R0 | R_0603_1608Metric_Pad0.98x0.95mm_HandSolder | 104.0875 | -70.99 | 0 | top
R92 | 1R0 | R_0603_1608Metric_Pad0.98x0.95mm_HandSolder | 104.0875 | -73.5 | 0 | top
R97 | 1R0 | R_0603_1608Metric_Pad0.98x0.95mm_HandSolder | 173.5 | -72.75 | 90 | top
R98 | 1R0 | R_0603_1608Metric_Pad0.98x0.95mm_HandSolder | 173.4125 | -61.54 | 90 | top
R99 | 1R0 | R_0603_1608Metric_Pad0.98x0.95mm_HandSolder | 162 | -149.25 | 90 | top
R100 | 1K | R_0603_1608Metric_Pad0.98x0.95mm_HandSolder | 179 | -84.38 | -90 | top
R101 | 10K | R_0603_1608Metric_Pad0.98x0.95mm_HandSolder | 96.25 | -88.5875 | -90 | top
R102 | 4K7 | R_0603_1608Metric_Pad0.98x0.95mm_HandSolder | 96.75 | -101.5 | 90 | top
R103 | 10K | R_0603_1608Metric_Pad0.98x0.95mm_HandSolder | 95.21 | -106.7875 | 90 | top
R104 | 10K | R_0603_1608Metric_Pad0.98x0.95mm_HandSolder | 96.75 | -106.75 | -90 | top
R105 | 10K | R_0603_1608Metric_Pad0.98x0.95mm_HandSolder | 96.25 | -85.0875 | 90 | top
R106 | 20K | R_0603_1608Metric_Pad0.98x0.95mm_HandSolder | 96.25 | -80.8375 | 90 | top
R107 | 10K | R_0603_1608Metric_Pad0.98x0.95mm_HandSolder | 95.25 | -110.3375 | -90 | top
R108 | 20K | R_0603_1608Metric_Pad0.98x0.95mm_HandSolder | 95.25 | -114 | -90 | top
R109 | 1R0 | R_0603_1608Metric_Pad0.98x0.95mm_HandSolder | 177.75 | -118.25 | 90 | top
R110 | 1R0 | R_0603_1608Metric_Pad0.98x0.95mm_HandSolder | 177.75 | -114.5 | 90 | top
R111 | 1R0 | R_0603_1608Metric_Pad0.98x0.95mm_HandSolder | 174.25 | -83.9675 | -90 | top
R112 | 1R0 | R_0603_1608Metric_Pad0.98x0.95mm_HandSolder | 168.75 | -148 | -90 | top
R113 | 10K | R_0603_1608Metric_Pad0.98x0.95mm_HandSolder | 173.5875 | -76.48 | -90 | top
R114 | 10K | R_0603_1608Metric_Pad0.98x0.95mm_HandSolder | 173.4125 | -65 | -90 | top
R115 | 1K | R_0603_1608Metric_Pad0.98x0.95mm_HandSolder | 176.3375 | -72.23 | 0 | top
R116 | 1K | R_0603_1608Metric_Pad0.98x0.95mm_HandSolder | 175.9125 | -61.5 | 0 | top
R117 | 1M | R_0603_1608Metric_Pad0.98x0.95mm_HandSolder | 67 | -44.5 | 90 | top
R118 | 1R0 | R_0603_1608Metric_Pad0.98x0.95mm_HandSolder | 101.75 | -45 | 90 | top
R119 | 1R0 | R_0603_1608Metric_Pad0.98x0.95mm_HandSolder | 70.5 | -44.4125 | 90 | top
R120 | DNI | R_0603_1608Metric_Pad0.98x0.95mm_HandSolder | 105.25 | -45 | 90 | top
R121 | 1R0 | R_0603_1608Metric_Pad0.98x0.95mm_HandSolder | 176.3375 | -80.75 | 0 | top
R122 | 1R0 | R_0603_1608Metric_Pad0.98x0.95mm_HandSolder | 176 | -69 | 0 | top
R123 | 10K | R_0603_1608Metric_Pad0.98x0.95mm_HandSolder | 170 | -169.1625 | 90 | top
R124 | 10K | R_0603_1608Metric_Pad0.98x0.95mm_HandSolder | 170 | -165.4125 | 90 | top
R125 | 4K7 | R_0603_1608Metric_Pad0.98x0.95mm_HandSolder | 170 | -161.6625 | -90 | top
R126 | 10K | R_0603_1608Metric_Pad0.98x0.95mm_HandSolder | 169.75 | -81.5 | -90 | top
R127 | 10K | R_0603_1608Metric_Pad0.98x0.95mm_HandSolder | 169.75 | -85.25 | -90 | top
R128 | 4K7 | R_0603_1608Metric_Pad0.98x0.95mm_HandSolder | 169.75 | -89 | 90 | top
R129 | 39R | R_0603_1608Metric_Pad0.98x0.95mm_HandSolder | 162.5 | -79.25 | 180 | top
R130 | 1K | R_0603_1608Metric_Pad0.98x0.95mm_HandSolder | 170 | -78.75 | 0 | top
R131 | 39R | R_0603_1608Metric_Pad0.98x0.95mm_HandSolder | 108 | -114 | 180 | top
R132 | 39R | R_0603_1608Metric_Pad0.98x0.95mm_HandSolder | 108 | -116.25 | 180 | top
R133 | 39R | R_0603_1608Metric_Pad0.98x0.95mm_HandSolder | 108 | -119 | 180 | top
R134 | 39R | R_0603_1608Metric_Pad0.98x0.95mm_HandSolder | 108 | -124 | 180 | top
R135 | 39R | R_0603_1608Metric_Pad0.98x0.95mm_HandSolder | 108 | -126.75 | 180 | top
R136 | 39R | R_0603_1608Metric_Pad0.98x0.95mm_HandSolder | 108 | -129.25 | 180 | top
R137 | 39R | R_0603_1608Metric_Pad0.98x0.95mm_HandSolder | 107.9125 | -132 | 180 | top
R138 | 39R | R_0603_1608Metric_Pad0.98x0.95mm_HandSolder | 162.3375 | -98.76 | 180 | top
R139 | 39R | R_0603_1608Metric_Pad0.98x0.95mm_HandSolder | 162.3375 | -96.25 | 180 | top
R140 | 1R0 | R_0603_1608Metric_Pad0.98x0.95mm_HandSolder | 170.25 | -172.25 | 0 | top
R141 | 1R0 | R_0603_1608Metric_Pad0.98x0.95mm_HandSolder | 175.5 | -95.25 | -90 | top
R142 | 10K | R_0603_1608Metric_Pad0.98x0.95mm_HandSolder | 169.8375 | -180 | 0 | top
R143 | 10K | R_0603_1608Metric_Pad0.98x0.95mm_HandSolder | 152.1805 | -105.5 | 0 | top
R144 | 1R0 | R_0603_1608Metric_Pad0.98x0.95mm_HandSolder | 127.201 | -168.564 | 180 | top
R145 | 1R0 | R_0603_1608Metric_Pad0.98x0.95mm_HandSolder | 119.581 | -167.548 | 90 | top
R146 | 1R0 | R_0603_1608Metric_Pad0.98x0.95mm_HandSolder | 123.137 | -168.564 | 180 | top
R147 | 1R0 | R_0603_1608Metric_Pad0.98x0.95mm_HandSolder | 162.2295 | -46.898 | 180 | top
R148 | 1R0 | R_0603_1608Metric_Pad0.98x0.95mm_HandSolder | 90.244 | -177.2 | 180 | top
R149 | 1R0 | R_0603_1608Metric_Pad0.98x0.95mm_HandSolder | 135.837 | -168.056 | 180 | top
R150 | 1R0 | R_0603_1608Metric_Pad0.98x0.95mm_HandSolder | 105.611 | -167.548 | 90 | top
R151 | 1R0 | R_0603_1608Metric_Pad0.98x0.95mm_HandSolder | 102.69 | -180.375 | 180 | top
R152 | 1R0 | R_0603_1608Metric_Pad0.98x0.95mm_HandSolder | 106.119 | -180.375 | 0 | top
R153 | 1R0 | R_0603_1608Metric_Pad0.98x0.95mm_HandSolder | 109.675 | -180.502 | 180 | top
R154 | 1R0 | R_0603_1608Metric_Pad0.98x0.95mm_HandSolder | 100.785 | -167.04 | 90 | top
R155 | 1R0 | R_0603_1608Metric_Pad0.98x0.95mm_HandSolder | 137.361 | -171.104 | -90 | top
R156 | 1R0 | R_0603_1608Metric_Pad0.98x0.95mm_HandSolder | 103.833 | -167.04 | -90 | top
R157 | 1R0 | R_0603_1608Metric_Pad0.98x0.95mm_HandSolder | 102.309 | -167.04 | -90 | top
R158 | 1R0 | R_0603_1608Metric_Pad0.98x0.95mm_HandSolder | 128.471 | -179.994 | 180 | top
R159 | 1R0 | R_0603_1608Metric_Pad0.98x0.95mm_HandSolder | 122.629 | -179.994 | 0 | top
R160 | 1R0 | R_0603_1608Metric_Pad0.98x0.95mm_HandSolder | 128.979 | -166.786 | 0 | top
R161 | 1R0 | R_0603_1608Metric_Pad0.98x0.95mm_HandSolder | 112.723 | -168.31 | 180 | top
R162 | 1R0 | R_0603_1608Metric_Pad0.98x0.95mm_HandSolder | 162.2295 | -49.692 | 180 | top
R163 | 1R0 | R_0603_1608Metric_Pad0.98x0.95mm_HandSolder | 162.2295 | -52.486 | 180 | top
R164 | 1R0 | R_0603_1608Metric_Pad0.98x0.95mm_HandSolder | 162.2295 | -55.534 | 180 | top
R165 | 1R0 | R_0603_1608Metric_Pad0.98x0.95mm_HandSolder | 72.464 | -162.976 | 90 | top
R166 | 1R0 | R_0603_1608Metric_Pad0.98x0.95mm_HandSolder | 73.988 | -176.438 | 90 | top
R167 | 4K7 | R_0603_1608Metric_Pad0.98x0.95mm_HandSolder | 158.4195 | -55.534 | 180 | top
R168 | 4K7 | R_0603_1608Metric_Pad0.98x0.95mm_HandSolder | 158.57 | -52.486 | 180 | top
R169 | 1R0 | R_0603_1608Metric_Pad0.98x0.95mm_HandSolder | 163.396 | -191.424 | 90 | top
R170 | 39R | R_0603_1608Metric_Pad0.98x0.95mm_HandSolder | 162.38 | -108.874 | 180 | top
R171 | 39R | R_0603_1608Metric_Pad0.98x0.95mm_HandSolder | 162.38 | -106.334 | 180 | top
R172 | 1K | R_0603_1608Metric_Pad0.98x0.95mm_HandSolder | 162.38 | -92.11 | 0 | top
R173 | 1K | R_0603_1608Metric_Pad0.98x0.95mm_HandSolder | 156.792 | -151.546 | -90 | top
R174 | 39R | R_0603_1608Metric_Pad0.98x0.95mm_HandSolder | 162.38 | -87.03 | 180 | top
R175 | 39R | R_0603_1608Metric_Pad0.98x0.95mm_HandSolder | 162.38 | -84.49 | 180 | top
R176 | 39R | R_0603_1608Metric_Pad0.98x0.95mm_HandSolder | 162.38 | -81.95 | 180 | top
R177 | 39R | R_0603_1608Metric_Pad0.98x0.95mm_HandSolder | 152.728 | -151.038 | 90 | top
R178 | 39R | R_0603_1608Metric_Pad0.98x0.95mm_HandSolder | 154.506 | -151.038 | 90 | top
R179 | 39R | R_0603_1608Metric_Pad0.98x0.95mm_HandSolder | 150.188 | -150.9345 | 90 | top
R180 | 10K | R_0603_1608Metric_Pad0.98x0.95mm_HandSolder | 102.055 | -130.287 | -90 | top
R181 | 4K7 | R_0603_1608Metric_Pad0.98x0.95mm_HandSolder | 102.055 | -134.1705 | 90 | top
R182 | 10K | R_0603_1608Metric_Pad0.98x0.95mm_HandSolder | 151.839 | -97.698 | 0 | top
R183 | 10K | R_0603_1608Metric_Pad0.98x0.95mm_HandSolder | 151.839 | -95.158 | 0 | top
R184 | 2K | R_0603_1608Metric_Pad0.98x0.95mm_HandSolder | 182.827 | -157.388 | 180 | top
R185 | 2K | R_0603_1608Metric_Pad0.98x0.95mm_HandSolder | 181.811 | -84.49 | 180 | top
R201 | 1K | R_0603_1608Metric_Pad0.98x0.95mm_HandSolder | 211.275 | -200.1635 | -90 | top
R202 | 1K | R_0603_1608Metric_Pad0.98x0.95mm_HandSolder | 208.511 | -200.1635 | -90 | top
R203 | 1K | R_0603_1608Metric_Pad0.98x0.95mm_HandSolder | 205.687 | -200.1635 | -90 | top
R204 | 1K | R_0603_1608Metric_Pad0.98x0.95mm_HandSolder | 202.893 | -200.1635 | -90 | top
R801 | 1R0 | R_0603_1608Metric_Pad0.98x0.95mm_HandSolder | 90.7285 | -175.168 | 0 | top
R802 | 10K | R_0603_1608Metric_Pad0.98x0.95mm_HandSolder | 191.209 | -193.8135 | 90 | top
R803 | 1K | R_0603_1608Metric_Pad0.98x0.95mm_HandSolder | 194.003 | -194.98 | 0 | top
R804 | 1R0 | R_0603_1608Metric_Pad0.98x0.95mm_HandSolder | 194.765 | -164.53 | 0 | top
R805 | DNI | R_0603_1608Metric_Pad0.98x0.95mm_HandSolder | 194.765 | -167.04 | 0 | top
R806 | 1R0 | R_0603_1608Metric_Pad0.98x0.95mm_HandSolder | 198.6785 | -190.916 | 0 | top
R807 | 1R0 | R_0603_1608Metric_Pad0.98x0.95mm_HandSolder | 194.765 | -169.072 | 180 | top
S1 | SWITCH_TACTILE_SPST-NO_0.05A_24V | Switch_Tactile_THT_6x6mm | 88.75 | -52.75 | 0 | top
S2 | SWITCH_TACTILE_SPST-NO_0.05A_24V | Switch_Tactile_THT_6x6mm | 68 | -219.75 | 180 | top
TP1 | GND | TestPoint_Loop_D2.54mm_Drill1.5mm_Beaded | 55 | -196.75 | 0 | top
TP2 | +12V | TestPoint_Loop_D2.54mm_Drill1.5mm_Beaded | 103.25 | -61 | 90 | top
TP3 | GND | TestPoint_Loop_D2.54mm_Drill1.5mm_Beaded | 103 | -65 | 0 | top
TP4 | GND | TestPoint_Loop_D2.54mm_Drill1.5mm_Beaded | 60.5 | -60 | 0 | top
TP5 | +VccMAX31850 | TestPoint_Loop_D2.54mm_Drill1.5mm_Beaded | 161.237 | -217.332 | 180 | top
TP6 | +VccMAX31850_1 | TestPoint_Loop_D2.54mm_Drill1.5mm_Beaded | 141 | -188.95 | 180 | top
TP7 | +VccMAX31850_2 | TestPoint_Loop_D2.54mm_Drill1.5mm_Beaded | 114.5 | -188.95 | 180 | top
TP8 | +VccMAX31850_3 | TestPoint_Loop_D2.54mm_Drill1.5mm_Beaded | 86 | -188.95 | 180 | top
TP9 | +VccMAX3185 | TestPoint_Loop_D2.54mm_Drill1.5mm_Beaded | 163 | -211.45 | 180 | top
TP10 | +VccMCP9600 | TestPoint_Loop_D2.54mm_Drill1.5mm_Beaded | 163 | -205.75 | 180 | top
TP11 | GND | TestPoint_Loop_D2.54mm_Drill1.5mm_Beaded | 53 | -120.5 | 0 | top
TP17 | I2C_VCC | TestPoint_Loop_D2.54mm_Drill1.5mm_Beaded | 63 | -163 | 90 | top
TP18 | SCL_5V | TestPoint_Loop_D2.54mm_Drill1.5mm_Beaded | 63.5 | -188 | 90 | top
TP19 | SDA_5V | TestPoint_Loop_D2.54mm_Drill1.5mm_Beaded | 68.5 | -163 | 0 | top
TP20 | +24V | TestPoint_Loop_D2.54mm_Drill1.5mm_Beaded | 64.5 | -54.75 | 0 | top
TP21 | GND | TestPoint_Loop_D2.54mm_Drill1.5mm_Beaded | 184.859 | -46.644 | 0 | top
TP201 | +VccMAX31850_3 | TestPoint_Loop_D2.54mm_Drill1.5mm_Beaded | 199.845 | -200.06 | 180 | top
TP999 | TestPoint | TestPoint_Loop_D2.54mm_Drill1.5mm_Beaded | 2.025 | -2.025 | 0 | top
TPSwitched_Fan_Power1 | Switched_Fan_Power | TestPoint_Loop_D2.54mm_Drill1.5mm_Beaded | 58 | -120.5 | 0 | top
TP_CIPO1 | CIPO | TestPoint_Loop_D2.54mm_Drill1.5mm_Beaded | 92.022 | -149.514 | 0 | top
TP_COPI1 | COPI | TestPoint_Loop_D2.54mm_Drill1.5mm_Beaded | 89.863 | -171.358 | 0 | top
TP_SCL1 | SCL | TestPoint_Loop_D2.54mm_Drill1.5mm_Beaded | 149.045 | -164.5 | 0 | top
TP_SCL2 | SCL1 | TestPoint_Loop_D2.54mm_Drill1.5mm_Beaded | 170.254 | -47.66 | 0 | top
TP_SDA1 | SDA | TestPoint_Loop_D2.54mm_Drill1.5mm_Beaded | 157.3 | -165.77 | 0 | top
TP_SDA2 | SDA1 | TestPoint_Loop_D2.54mm_Drill1.5mm_Beaded | 165.682 | -59.344 | 0 | top
TP_SD_DET1 | TP_SD_DET | TestPoint_Loop_D2.54mm_Drill1.5mm_Beaded | 97.991 | -166.532 | 0 | top
TP_SPI_SCK1 | SPI_SCK | TestPoint_Loop_D2.54mm_Drill1.5mm_Beaded | 85.291 | -170.342 | 0 | top
TP_VIN1 | VIN1 | TestPoint_Loop_D2.54mm_Drill1.5mm_Beaded | 97.61 | -64.932 | 0 | top

Sheet: JLCPCB_PL&POS
*_Comment101 | *_Designator | Footprint | JLCPCB Part # | Designator | Mid X | Mid Y | Layer | Rotation
0 | 0 | 0 | 0 | 0 | 92.403 | -124.622 | 0 | 0
0 | 0 | 0 | 0 | 0 | 93.165 | -93.38 | 0 | 0
0 | 0 | 0 | 0 | 0 | 167.079 | -185.328 | 0 | 0
0 | 0 | 0 | 0 | 0 | 63.1 | -182 | 0 | -90
0 | 0 | 0 | 0 | 0 | 63.75 | -168.75 | 0 | 180
0 | 0 | 0 | 0 | 0 | 64.1375 | -86.75 | 0 | 180
0 | 0 | 0 | 0 | 0 | 64 | -82 | 0 | 0
0 | 0 | 0 | 0 | 0 | 64.1375 | -89.8 | 0 | 180
0 | 0 | 0 | 0 | 0 | 63.9375 | -92.4 | 0 | 180
0 | 0 | 0 | 0 | 0 | 63.9375 | -95.2 | 0 | 180
0 | 0 | 0 | 0 | 0 | 63.9375 | -107 | 0 | 180
0 | 0 | 0 | 0 | 0 | 64.5 | -103.75 | 0 | 180
0 | 0 | 0 | 0 | 0 | 64.1375 | -100.6 | 0 | 180
0 | 0 | 0 | 0 | 0 | 64.1375 | -98 | 0 | 180
0 | 0 | 0 | 0 | 0 | 75.8625 | -162.5 | 0 | 180
0 | 0 | 0 | 0 | 0 | 67.86875 | -174.5 | 0 | 90
0 | 0 | 0 | 0 | 0 | 63 | -178 | 0 | 90
0 | 0 | 0 | 0 | 0 | 63 | -174 | 0 | -90
0 | 0 | 0 | 0 | 0 | 179.017 | -38.77 | 0 | -90
0 | 0 | 0 | 0 | 0 | 93 | -65.5 | 0 | 180
0 | 0 | 0 | 0 | 0 | 116.279 | -168.056 | 0 | 0
0 | 0 | 0 | 0 | 0 | 75 | -113 | 0 | 0
0 | 0 | 0 | 0 | 0 | 74.19 | -92.5 | 0 | 0
0 | 0 | 0 | 0 | 0 | 101.75 | -82.25 | 0 | 90
0 | 0 | 0 | 0 | 0 | 170.25 | -75.5 | 0 | 0
0 | 0 | 0 | 0 | 0 | 215.339 | -174.66 | 0 | 90
0 | 0 | 0 | 0 | 0 | 166 | -141.3 | 0 | 0
0 | 0 | 0 | 0 | 0 | 183.843 | -123.352 | 0 | 0
0 | 0 | 0 | 0 | 0 | 171.25 | -141.25 | 0 | 0
0 | 0 | 0 | 0 | 0 | 176.731 | -122.25 | 0 | 0
0 | 0 | 0 | 0 | 0 | 216.6345 | -187.868 | 0 | 180
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
0 | 0 | 0 | 0 | 0 | 170.254 | -47.66 | 0 | 0
0 | 0 | 0 | 0 | 0 | 157.3 | -165.77 | 0 | 0
0 | 0 | 0 | 0 | 0 | 165.682 | -59.344 | 0 | 0
0 | 0 | 0 | 0 | 0 | 97.991 | -166.532 | 0 | 0
0 | 0 | 0 | 0 | 0 | 85.291 | -170.342 | 0 | 0
0 | 0 | 0 | 0 | 0 | 97.61 | -64.932 | 0 | 0

Sheet: PL&POS_Reduced
Comment | Designator | Footprint | JLCPCB Part # | Designator | Mid X | Mid Y | Layer | Rotation
+3.3V | +3.3V101 | TestPoint:TestPoint_Loop_D2.54mm_Drill1.5mm_Beaded | C5277086 | +3.3V101 | 92.403 | -124.622 | top | 0
+5V | +5V101 | TestPoint:TestPoint_Loop_D2.54mm_Drill1.5mm_Beaded | C5277086 | +5V101 | 93.165 | -93.38 | top | 0
5VHead | 5VHead101 | TestPoint:TestPoint_Loop_D2.54mm_Drill1.5mm_Beaded | C5277086 | 5VHead101 | 167.079 | -185.328 | top | 0
39pF | C1 | Capacitor_SMD:C_0603_1608Metric_Pad1.08x0.95mm_HandSolder | C107049 | C1 | 63.1 | -182 | top | -90
39pF | C2 | Capacitor_SMD:C_0603_1608Metric_Pad1.08x0.95mm_HandSolder | C107049 | C2 | 63.75 | -168.75 | top | 180
39pF | C3 | Capacitor_SMD:C_0603_1608Metric_Pad1.08x0.95mm_HandSolder | C107049 | C3 | 64.1375 | -86.75 | top | 180
39pF | C4 | Capacitor_SMD:C_0603_1608Metric_Pad1.08x0.95mm_HandSolder | C107049 | C4 | 64 | -82 | top | 0
39pF | C5 | Capacitor_SMD:C_0603_1608Metric_Pad1.08x0.95mm_HandSolder | C107049 | C5 | 64.1375 | -89.8 | top | 180
39pF | C6 | Capacitor_SMD:C_0603_1608Metric_Pad1.08x0.95mm_HandSolder | C107049 | C6 | 63.9375 | -92.4 | top | 180
39pF | C7 | Capacitor_SMD:C_0603_1608Metric_Pad1.08x0.95mm_HandSolder | C107049 | C7 | 63.9375 | -95.2 | top | 180
39pF | C8 | Capacitor_SMD:C_0603_1608Metric_Pad1.08x0.95mm_HandSolder | C107049 | C8 | 63.9375 | -107 | top | 180
39pF | C9 | Capacitor_SMD:C_0603_1608Metric_Pad1.08x0.95mm_HandSolder | C107049 | C9 | 64.5 | -103.75 | top | 180
39pF | C10 | Capacitor_SMD:C_0603_1608Metric_Pad1.08x0.95mm_HandSolder | C107049 | C10 | 64.1375 | -100.6 | top | 180
39pF | C11 | Capacitor_SMD:C_0603_1608Metric_Pad1.08x0.95mm_HandSolder | C107049 | C11 | 64.1375 | -98 | top | 180
1uF | C18 | Capacitor_SMD:C_0603_1608Metric_Pad1.08x0.95mm_HandSolder | C91183 | C18 | 75.8625 | -162.5 | top | 180
1uF | C19 | Capacitor_SMD:C_0603_1608Metric_Pad1.08x0.95mm_HandSolder | C91183 | C19 | 67.86875 | -174.5 | top | 90
39pF | C20 | Capacitor_SMD:C_0603_1608Metric_Pad1.08x0.95mm_HandSolder | C107049 | C20 | 63 | -178 | top | 90
39pF | C21 | Capacitor_SMD:C_0603_1608Metric_Pad1.08x0.95mm_HandSolder | C107049 | C21 | 63 | -174 | top | -90
10nF | C22 | Capacitor_SMD:C_0603_1608Metric_Pad1.08x0.95mm_HandSolder | C389113 | C22 | 179.017 | -38.77 | top | -90
39pF | C23 | Capacitor_SMD:C_0603_1608Metric_Pad1.08x0.95mm_HandSolder | C107049 | C23 | 93 | -65.5 | top | 180
1uF | C24 | Capacitor_SMD:C_0603_1608Metric_Pad1.08x0.95mm_HandSolder | C91183 | C24 | 116.279 | -168.056 | top | 0
5.1V | D1 | Diode_SMD:D_MiniMELF | C2857227 | D1 | 75 | -113 | top | 0
5.1V | D2 | Diode_SMD:D_MiniMELF | C2857227 | D2 | 74.19 | -92.5 | top | 0
1N5819WS | D3 | Diode_SMD:D_SOD-323 | C191023 | D3 | 101.75 | -82.25 | top | 90
RED 0603 | D4 | LED_SMD:LED_0603_1608Metric_Pad1.05x0.95mm_HandSolder | C2286 | D4 | 170.25 | -75.5 | top | 0
1N5819WS | D801 | Diode_SMD:D_SOD-323 | C191023 | D801 | 215.339 | -174.66 | top | 90
D_PSU_RX | D_PSU_RX1 | TestPoint:TestPoint_Loop_D2.54mm_Drill1.5mm_Beaded | C5199807 | D_PSU_RX1 | 166 | -141.3 | top | 0
D_PSU_RX2 | D_PSU_RX2 | TestPoint:TestPoint_Loop_D2.54mm_Drill1.5mm_Beaded | C5199807 | D_PSU_RX2 | 183.843 | -123.352 | top | 0
D_PSU_TX | D_PSU_TX1 | TestPoint:TestPoint_Loop_D2.54mm_Drill1.5mm_Beaded | C5199812 | D_PSU_TX1 | 171.25 | -141.25 | top | 0
D_PSU_TX2 | D_PSU_TX2 | TestPoint:TestPoint_Loop_D2.54mm_Drill1.5mm_Beaded | C5199812 | D_PSU_TX2 | 176.731 | -122.25 | top | 0
Polyfuse_0603_1A | F801 | Fuse:Fuse_0603_1608Metric | C207017 | F801 | 216.6345 | -187.868 | top | 180
Conn_02x12_Odd_Even | J10 | PubInv_KiCad_PCB:JST_PHD_B24B-PHDSS_2x12_P2.00mm_Vertical | C160327 | J10 | 177.493 | -184.566 | top | 90
Con_01x02_2.5mm | J11 | PubInv_KiCad_PCB:JST_XH_B2B-XH-AM_1x02_P2.50mm_Vertical | C265283 | J11 | 101.73 | -55 | top | 0
Con_01x02_2.5mm | J12 | PubInv_KiCad_PCB:JST_XH_B2B-XH-AM_1x02_P2.50mm_Vertical | C265283 | J12 | 70.23 | -55 | top | 0
Con_01x02_2.5mm | J13 | PubInv_KiCad_PCB:JST_XH_B2B-XH-AM_1x02_P2.50mm_Vertical | C265283 | J13 | 80 | -55 | top | 0
Con_01x02_0.1" | J23 | Connector_PinHeader_2.54mm:PinHeader_1x02_P2.54mm_Vertical | C492401 | J23 | 66.46 | -156 | top | 90
Conn_01x04 | J24 | Connector_PinHeader_2.54mm:PinHeader_1x04_P2.54mm_Vertical | C6332197 | J24 | 53.38 | -157 | top | 90
Con_01x02_2.5mm | J25 | PubInv_KiCad_PCB:JST_XH_B2B-XH-AM_1x02_P2.50mm_Vertical | C265283 | J25 | 183.5 | -190 | top | -90
Con_01x02_2.5mm | J28 | PubInv_KiCad_PCB:JST_XH_B2B-XH-AM_1x02_P2.50mm_Vertical | C265283 | J28 | 182.59 | -115.752 | top | -90
Con_01x02_2.5mm | J30 | PubInv_KiCad_PCB:JST_XH_B2B-XH-AM_1x02_P2.50mm_Vertical | C265283 | J30 | 182.0875 | -77.23 | top | -90
Con_01x02_2.5mm | J31 | PubInv_KiCad_PCB:JST_XH_B2B-XH-AM_1x02_P2.50mm_Vertical | C265283 | J31 | 182 | -65.71 | top | -90
Con_01x02_2.5mm | J32 | PubInv_KiCad_PCB:JST_XH_B2B-XH-AM_1x02_P2.50mm_Vertical | C265283 | J32 | 178.235 | -217.603 | top | 180
Con_01x02_2.5mm | J33 | PubInv_KiCad_PCB:JST_XH_B2B-XH-AM_1x02_P2.50mm_Vertical | C265283 | J33 | 169.599 | -217.603 | top | 180
Con_01x02_2.5mm | J34 | PubInv_KiCad_PCB:JST_XH_B2B-XH-AM_1x02_P2.50mm_Vertical | C265283 | J34 | 75.893 | -217.84 | top | 180
Conn_01x04 | J37 | Connector_PinHeader_2.54mm:PinHeader_1x04_P2.54mm_Vertical | C6332197 | J37 | 165.7855 | -47.152 | top | 0
Con_01x02_2.5mm | J201 | PubInv_KiCad_PCB:JST_XH_B2B-XH-AM_1x02_P2.50mm_Vertical | C265283 | J201 | 221.669 | -219.635 | top | 180
Conn_01x03_0.1" | J801 | Connector_PinHeader_2.54mm:PinHeader_1x03_P2.54mm_Vertical | C6332196 | J801 | 142.441 | -168.31 | top | 0
Con_01x02_0.1" | J802 | Connector_PinHeader_2.54mm:PinHeader_1x02_P2.54mm_Vertical | C492401 | J802 | 148.029 | -172.12 | top | 0
Screw_Terminal_01x02_5.08mm | J804 | TerminalBlock_Phoenix:TerminalBlock_Phoenix_MKDS-1,5-2-5.08_1x02_P5.08mm_Horizontal | C5142622 | J804 | 224.991 | -193.456 | top | 90
Con_01x02_0.1" | J805 | Connector_PinHeader_2.54mm:PinHeader_1x02_P2.54mm_Vertical | C492401 | J805 | 152.679 | 172.12 | top | 0
MAX31850K | JP9 | PubInv_KiCad_PCB:Adafruit_MAX31850K_Module | C2905417 | JP9 | 155 | -193.95 | top | 180
MAX31850K | JP10 | PubInv_KiCad_PCB:Adafruit_MAX31850K_Module | C2905417 | JP10 | 127.725 | -193.95 | top | 180
MAX31850K | JP15 | PubInv_KiCad_PCB:Adafruit_MAX31850K_Module | C2905417 | JP15 | 100.28 | -193.95 | top | 180
MAX31850K | JP205 | PubInv_KiCad_PCB:Adafruit_MAX31850K_Module | C2905417 | JP205 | 213.546 | -204.04448 | top | 180
Relay SRU-12VDC | K801 | Relay_THT:Relay_SPDT_Omron-G5LE-1 | C47402 | K801 | 211.275 | -179.74 | top | -90
BSS138 | Q1 | Package_TO_SOT_SMD:SOT-23 | C400505 | Q1 | 78.4375 | -116 | top | 180
NCE01P30K | Q2 | Package_TO_SOT_SMD:TO-252-2 | C115991 | Q2 | 71.5 | -73.565 | top | -90
BSS138 | Q3 | Package_TO_SOT_SMD:SOT-23 | C400505 | Q3 | 78.5 | -71 | top | 180
BSS138 | Q4 | Package_TO_SOT_SMD:SOT-23 | C400505 | Q4 | 76.25 | -61.25 | top | 180
BSS138 | Q9 | Package_TO_SOT_SMD:SOT-23 | C400505 | Q9 | 70.55 | -187.85 | top | -90
BSS138 | Q10 | Package_TO_SOT_SMD:SOT-23 | C400505 | Q10 | 70.4625 | -171.39375 | top | -90
BSS138 | Q11 | Package_TO_SOT_SMD:SOT-23 | C400505 | Q11 | 176.3375 | -76.5 | top | 0
BSS138 | Q12 | Package_TO_SOT_SMD:SOT-23 | C400505 | Q12 | 176.25 | -65 | top | 0
BSS138 | Q13 | Package_TO_SOT_SMD:SOT-23 | C400505 | Q13 | 170 | -175.5 | top | 90
BSS138 | Q14 | Package_TO_SOT_SMD:SOT-23 | C400505 | Q14 | 152.093 | -101 | top | 90
BSS138 | Q801 | Package_TO_SOT_SMD:SOT-23 | C400505 | Q801 | 194.511 | -190.8375 | top | 90
1R0 | R1 | Resistor_SMD:R_0603_1608Metric_Pad0.98x0.95mm_HandSolder | C269434 | R1 | 105.992 | -188.376 | top | -90
1R0 | R2 | Resistor_SMD:R_0603_1608Metric_Pad0.98x0.95mm_HandSolder | C269434 | R2 | 159.5 | -191.95 | top | -90
1R0 | R3 | Resistor_SMD:R_0603_1608Metric_Pad0.98x0.95mm_HandSolder | C269434 | R3 | 129.5 | -187.394 | top | -90
1R0 | R4 | Resistor_SMD:R_0603_1608Metric_Pad0.98x0.95mm_HandSolder | C269434 | R4 | 156.5 | -188.3625 | top | -90
1R0 | R5 | Resistor_SMD:R_0603_1608Metric_Pad0.98x0.95mm_HandSolder | C269434 | R5 | 83.5 | -176.5 | top | -90
1R0 | R6 | Resistor_SMD:R_0603_1608Metric_Pad0.98x0.95mm_HandSolder | C269434 | R6 | 86.5 | -176.5 | top | -90
1R0 | R7 | Resistor_SMD:R_0603_1608Metric_Pad0.98x0.95mm_HandSolder | C269434 | R7 | 134 | -186.344 | top | -90
1R0 | R8 | Resistor_SMD:R_0603_1608Metric_Pad0.98x0.95mm_HandSolder | C269434 | R8 | 64 | -167 | top | 0
1R0 | R9 | Resistor_SMD:R_0603_1608Metric_Pad0.98x0.95mm_HandSolder | C269434 | R9 | 80.5 | -63.5 | top | 180
1R0 | R10 | Resistor_SMD:R_0603_1608Metric_Pad0.98x0.95mm_HandSolder | C269434 | R10 | 82.9125 | -75.25 | top | 0
1R0 | R11 | Resistor_SMD:R_0603_1608Metric_Pad0.98x0.95mm_HandSolder | C269434 | R11 | 86.25 | -121.75 | top | 0
1R0 | R12 | Resistor_SMD:R_0603_1608Metric_Pad0.98x0.95mm_HandSolder | C269434 | R12 | 79 | -120 | top | 0
1R0 | R13 | Resistor_SMD:R_0603_1608Metric_Pad0.98x0.95mm_HandSolder | C269434 | R13 | 164.5 | -148 | top | 90
1K | R14 | Resistor_SMD:R_0603_1608Metric_Pad0.98x0.95mm_HandSolder | C269704 | R14 | 171.5 | -148 | top | -90
1R0 | R15 | Resistor_SMD:R_0603_1608Metric_Pad0.98x0.95mm_HandSolder | C269434 | R15 | 173.5 | -148 | top | -90
1R0 | R16 | Resistor_SMD:R_0603_1608Metric_Pad0.98x0.95mm_HandSolder | C269434 | R16 | 167 | -148 | top | -90
1K | R18 | Resistor_SMD:R_0603_1608Metric_Pad0.98x0.95mm_HandSolder | C269704 | R18 | 153 | -188.25 | top | -90
1K | R19 | Resistor_SMD:R_0603_1608Metric_Pad0.98x0.95mm_HandSolder | C269704 | R19 | 150 | -188.25 | top | -90
1K | R20 | Resistor_SMD:R_0603_1608Metric_Pad0.98x0.95mm_HandSolder | C269704 | R20 | 147 | -188.2 | top | -90
1K | R21 | Resistor_SMD:R_0603_1608Metric_Pad0.98x0.95mm_HandSolder | C269704 | R21 | 125.16 | -188.175 | top | -90
1K | R22 | Resistor_SMD:R_0603_1608Metric_Pad0.98x0.95mm_HandSolder | C269704 | R22 | 144 | -188.2 | top | -90
1K | R23 | Resistor_SMD:R_0603_1608Metric_Pad0.98x0.95mm_HandSolder | C269704 | R23 | 122.65 | -188.175 | top | -90
1K | R24 | Resistor_SMD:R_0603_1608Metric_Pad0.98x0.95mm_HandSolder | C269704 | R24 | 120.14 | -188.175 | top | -90
1K | R25 | Resistor_SMD:R_0603_1608Metric_Pad0.98x0.95mm_HandSolder | C269704 | R25 | 117.295 | -188.175 | top | -90
1K | R26 | Resistor_SMD:R_0603_1608Metric_Pad0.98x0.95mm_HandSolder | C269704 | R26 | 98.5 | -189.12302 | top | -90
1K | R27 | Resistor_SMD:R_0603_1608Metric_Pad0.98x0.95mm_HandSolder | C269704 | R27 | 95.5 | -189.12302 | top | -90
1K | R28 | Resistor_SMD:R_0603_1608Metric_Pad0.98x0.95mm_HandSolder | C269704 | R28 | 92.5 | -189.12302 | top | -90
1K | R29 | Resistor_SMD:R_0603_1608Metric_Pad0.98x0.95mm_HandSolder | C269704 | R29 | 89.47 | -189.21052 | top | -90
1R0 | R31 | Resistor_SMD:R_0603_1608Metric_Pad0.98x0.95mm_HandSolder | C269434 | R31 | 160 | -196.45 | top | -90
4M7 | R32 | Resistor_SMD:R_0603_1608Metric_Pad0.98x0.95mm_HandSolder | C23163 | R32 | 175.517 | -38.77 | top | -90
1R0 | R33 | Resistor_SMD:R_0603_1608Metric_Pad0.98x0.95mm_HandSolder | C269434 | R33 | 69.5 | -108.5 | top | 0
1K | R36 | Resistor_SMD:R_0603_1608Metric_Pad0.98x0.95mm_HandSolder | C269704 | R36 | 74.1625 | -116.75 | top | 0
1K | R37 | Resistor_SMD:R_0603_1608Metric_Pad0.98x0.95mm_HandSolder | C269704 | R37 | 78.25 | -124.25 | top | 0
1K | R38 | Resistor_SMD:R_0603_1608Metric_Pad0.98x0.95mm_HandSolder | C269704 | R38 | 81.5625 | -115.95 | top | 90
10K | R39 | Resistor_SMD:R_0603_1608Metric_Pad0.98x0.95mm_HandSolder | C269701 | R39 | 69.525 | -65.5 | top | 0
10K | R40 | Resistor_SMD:R_0603_1608Metric_Pad0.98x0.95mm_HandSolder | C269701 | R40 | 78 | -67.5 | top | 0
10K | R41 | Resistor_SMD:R_0603_1608Metric_Pad0.98x0.95mm_HandSolder | C269701 | R41 | 82 | -121.75 | top | 180
1K | R42 | Resistor_SMD:R_0603_1608Metric_Pad0.98x0.95mm_HandSolder | C269704 | R42 | 82 | -125 | top | 180
10K | R44 | Resistor_SMD:R_0603_1608Metric_Pad0.98x0.95mm_HandSolder | C269701 | R44 | 73.525 | -65.5 | top | 0
1K | R45 | Resistor_SMD:R_0603_1608Metric_Pad0.98x0.95mm_HandSolder | C269704 | R45 | 82.9125 | -72 | top | 0
10K | R46 | Resistor_SMD:R_0603_1608Metric_Pad0.98x0.95mm_HandSolder | C269701 | R46 | 83 | -69 | top | 180
1K | R47 | Resistor_SMD:R_0603_1608Metric_Pad0.98x0.95mm_HandSolder | C269704 | R47 | 80.5 | -60.5 | top | 180
1R0 | R48 | Resistor_SMD:R_0603_1608Metric_Pad0.98x0.95mm_HandSolder | C269434 | R48 | 71.5 | -60.5 | top | 180
1R0 | R66 | Resistor_SMD:R_0603_1608Metric_Pad0.98x0.95mm_HandSolder | C269434 | R66 | 79.5 | -162.5 | top | 180
10K | R67 | Resistor_SMD:R_0603_1608Metric_Pad0.98x0.95mm_HandSolder | C269701 | R67 | 70.4125 | -183.9125 | top | 180
10K | R68 | Resistor_SMD:R_0603_1608Metric_Pad0.98x0.95mm_HandSolder | C269701 | R68 | 70.4125 | -167.45625 | top | 180
10K | R69 | Resistor_SMD:R_0603_1608Metric_Pad0.98x0.95mm_HandSolder | C269701 | R69 | 69.7 | -191.8125 | top | 0
10K | R70 | Resistor_SMD:R_0603_1608Metric_Pad0.98x0.95mm_HandSolder | C269701 | R70 | 70.4125 | -175.45625 | top | 0
39R | R71 | Resistor_SMD:R_0603_1608Metric_Pad0.98x0.95mm_HandSolder | C325713 | R71 | 69.7 | -194.8125 | top | 0
39R | R72 | Resistor_SMD:R_0603_1608Metric_Pad0.98x0.95mm_HandSolder | C325713 | R72 | 70.5 | -178.45625 | top | 0
1R0 | R73 | Resistor_SMD:R_0603_1608Metric_Pad0.98x0.95mm_HandSolder | C269434 | R73 | 60.51 | -153.0875 | top | -90
1R0 | R76 | Resistor_SMD:R_0603_1608Metric_Pad0.98x0.95mm_HandSolder | C269434 | R76 | 97.5 | -61 | top | -90
4K7 | R77 | Resistor_SMD:R_0603_1608Metric_Pad0.98x0.95mm_HandSolder | C23162 | R77 | 92.5 | -154.0875 | top | 90
4K7 | R78 | Resistor_SMD:R_0603_1608Metric_Pad0.98x0.95mm_HandSolder | C23162 | R78 | 89 | -154.0875 | top | 90
1R0 | R79 | Resistor_SMD:R_0603_1608Metric_Pad0.98x0.95mm_HandSolder | C269434 | R79 | 175 | -189.75 | top | 90
1R0 | R80 | Resistor_SMD:R_0603_1608Metric_Pad0.98x0.95mm_HandSolder | C269434 | R80 | 178.25 | -189.75 | top | 90
10K | R81 | Resistor_SMD:R_0603_1608Metric_Pad0.98x0.95mm_HandSolder | C269701 | R81 | 84.5 | -60.5 | top | 0
1R0 | R82 | Resistor_SMD:R_0603_1608Metric_Pad0.98x0.95mm_HandSolder | C269434 | R82 | 161 | -187.95 | top | 90
4K7 | R83 | Resistor_SMD:R_0603_1608Metric_Pad0.98x0.95mm_HandSolder | C23162 | R83 | 101.5 | -188.95 | top | 90
1R0 | R84 | Resistor_SMD:R_0603_1608Metric_Pad0.98x0.95mm_HandSolder | C269434 | R84 | 160 | -201 | top | -90
1R0 | R88 | Resistor_SMD:R_0603_1608Metric_Pad0.98x0.95mm_HandSolder | C269434 | R88 | 67.5 | -61.5 | top | 0
1R0 | R91 | Resistor_SMD:R_0603_1608Metric_Pad0.98x0.95mm_HandSolder | C269434 | R91 | 104.0875 | -70.99 | top | 0
1R0 | R92 | Resistor_SMD:R_0603_1608Metric_Pad0.98x0.95mm_HandSolder | C269434 | R92 | 104.0875 | -73.5 | top | 0
1R0 | R97 | Resistor_SMD:R_0603_1608Metric_Pad0.98x0.95mm_HandSolder | C269434 | R97 | 173.5 | -72.75 | top | 90
1R0 | R98 | Resistor_SMD:R_0603_1608Metric_Pad0.98x0.95mm_HandSolder | C269434 | R98 | 173.4125 | -61.54 | top | 90
1R0 | R99 | Resistor_SMD:R_0603_1608Metric_Pad0.98x0.95mm_HandSolder | C269434 | R99 | 162 | -149.25 | top | 90
1K | R100 | Resistor_SMD:R_0603_1608Metric_Pad0.98x0.95mm_HandSolder | C269704 | R100 | 179 | -84.38 | top | -90
10K | R101 | Resistor_SMD:R_0603_1608Metric_Pad0.98x0.95mm_HandSolder | C269701 | R101 | 96.25 | -88.5875 | top | -90
4K7 | R102 | Resistor_SMD:R_0603_1608Metric_Pad0.98x0.95mm_HandSolder | C23162 | R102 | 96.75 | -101.5 | top | 90
10K | R103 | Resistor_SMD:R_0603_1608Metric_Pad0.98x0.95mm_HandSolder | C269701 | R103 | 95.21 | -106.7875 | top | 90
10K | R104 | Resistor_SMD:R_0603_1608Metric_Pad0.98x0.95mm_HandSolder | C269701 | R104 | 96.75 | -106.75 | top | -90
10K | R105 | Resistor_SMD:R_0603_1608Metric_Pad0.98x0.95mm_HandSolder | C269701 | R105 | 96.25 | -85.0875 | top | 90
20K | R106 | Resistor_SMD:R_0603_1608Metric_Pad0.98x0.95mm_HandSolder | C25804 | R106 | 96.25 | -80.8375 | top | 90
10K | R107 | Resistor_SMD:R_0603_1608Metric_Pad0.98x0.95mm_HandSolder | C269701 | R107 | 95.25 | -110.3375 | top | -90
20K | R108 | Resistor_SMD:R_0603_1608Metric_Pad0.98x0.95mm_HandSolder | C25804 | R108 | 95.25 | -114 | top | -90
1R0 | R109 | Resistor_SMD:R_0603_1608Metric_Pad0.98x0.95mm_HandSolder | C269434 | R109 | 177.75 | -118.25 | top | 90
1R0 | R110 | Resistor_SMD:R_0603_1608Metric_Pad0.98x0.95mm_HandSolder | C269434 | R110 | 177.75 | -114.5 | top | 90
1R0 | R111 | Resistor_SMD:R_0603_1608Metric_Pad0.98x0.95mm_HandSolder | C269434 | R111 | 174.25 | -83.9675 | top | -90
1R0 | R112 | Resistor_SMD:R_0603_1608Metric_Pad0.98x0.95mm_HandSolder | C269434 | R112 | 168.75 | -148 | top | -90
10K | R113 | Resistor_SMD:R_0603_1608Metric_Pad0.98x0.95mm_HandSolder | C269701 | R113 | 173.5875 | -76.48 | top | -90
10K | R114 | Resistor_SMD:R_0603_1608Metric_Pad0.98x0.95mm_HandSolder | C269701 | R114 | 173.4125 | -65 | top | -90
1K | R115 | Resistor_SMD:R_0603_1608Metric_Pad0.98x0.95mm_HandSolder | C269704 | R115 | 176.3375 | -72.23 | top | 0
1K | R116 | Resistor_SMD:R_0603_1608Metric_Pad0.98x0.95mm_HandSolder | C269704 | R116 | 175.9125 | -61.5 | top | 0
1R0 | R118 | Resistor_SMD:R_0603_1608Metric_Pad0.98x0.95mm_HandSolder | C269434 | R118 | 101.75 | -45 | top | 90
1R0 | R119 | Resistor_SMD:R_0603_1608Metric_Pad0.98x0.95mm_HandSolder | C269434 | R119 | 70.5 | -44.4125 | top | 90
1R0 | R121 | Resistor_SMD:R_0603_1608Metric_Pad0.98x0.95mm_HandSolder | C269434 | R121 | 176.3375 | -80.75 | top | 0
1R0 | R122 | Resistor_SMD:R_0603_1608Metric_Pad0.98x0.95mm_HandSolder | C269434 | R122 | 176 | -69 | top | 0
10K | R123 | Resistor_SMD:R_0603_1608Metric_Pad0.98x0.95mm_HandSolder | C269701 | R123 | 170 | -169.1625 | top | 90
10K | R124 | Resistor_SMD:R_0603_1608Metric_Pad0.98x0.95mm_HandSolder | C269701 | R124 | 170 | -165.4125 | top | 90
4K7 | R125 | Resistor_SMD:R_0603_1608Metric_Pad0.98x0.95mm_HandSolder | C23162 | R125 | 170 | -161.6625 | top | -90
10K | R126 | Resistor_SMD:R_0603_1608Metric_Pad0.98x0.95mm_HandSolder | C269701 | R126 | 169.75 | -81.5 | top | -90
10K | R127 | Resistor_SMD:R_0603_1608Metric_Pad0.98x0.95mm_HandSolder | C269701 | R127 | 169.75 | -85.25 | top | -90
4K7 | R128 | Resistor_SMD:R_0603_1608Metric_Pad0.98x0.95mm_HandSolder | C23162 | R128 | 169.75 | -89 | top | 90
39R | R129 | Resistor_SMD:R_0603_1608Metric_Pad0.98x0.95mm_HandSolder | C325713 | R129 | 162.5 | -79.25 | top | 180
1K | R130 | Resistor_SMD:R_0603_1608Metric_Pad0.98x0.95mm_HandSolder | C269704 | R130 | 170 | -78.75 | top | 0
39R | R131 | Resistor_SMD:R_0603_1608Metric_Pad0.98x0.95mm_HandSolder | C325713 | R131 | 108 | -114 | top | 180
39R | R132 | Resistor_SMD:R_0603_1608Metric_Pad0.98x0.95mm_HandSolder | C325713 | R132 | 108 | -116.25 | top | 180
39R | R133 | Resistor_SMD:R_0603_1608Metric_Pad0.98x0.95mm_HandSolder | C325713 | R133 | 108 | -119 | top | 180
39R | R134 | Resistor_SMD:R_0603_1608Metric_Pad0.98x0.95mm_HandSolder | C325713 | R134 | 108 | -124 | top | 180
39R | R135 | Resistor_SMD:R_0603_1608Metric_Pad0.98x0.95mm_HandSolder | C325713 | R135 | 108 | -126.75 | top | 180
39R | R136 | Resistor_SMD:R_0603_1608Metric_Pad0.98x0.95mm_HandSolder | C325713 | R136 | 108 | -129.25 | top | 180
39R | R137 | Resistor_SMD:R_0603_1608Metric_Pad0.98x0.95mm_HandSolder | C325713 | R137 | 107.9125 | -132 | top | 180
39R | R138 | Resistor_SMD:R_0603_1608Metric_Pad0.98x0.95mm_HandSolder | C325713 | R138 | 162.3375 | -98.76 | top | 180
39R | R139 | Resistor_SMD:R_0603_1608Metric_Pad0.98x0.95mm_HandSolder | C325713 | R139 | 162.3375 | -96.25 | top | 180
1R0 | R140 | Resistor_SMD:R_0603_1608Metric_Pad0.98x0.95mm_HandSolder | C269434 | R140 | 170.25 | -172.25 | top | 0
1R0 | R141 | Resistor_SMD:R_0603_1608Metric_Pad0.98x0.95mm_HandSolder | C269434 | R141 | 175.5 | -95.25 | top | -90
10K | R142 | Resistor_SMD:R_0603_1608Metric_Pad0.98x0.95mm_HandSolder | C269701 | R142 | 169.8375 | -180 | top | 0
10K | R143 | Resistor_SMD:R_0603_1608Metric_Pad0.98x0.95mm_HandSolder | C269701 | R143 | 152.1805 | -105.5 | top | 0
1R0 | R144 | Resistor_SMD:R_0603_1608Metric_Pad0.98x0.95mm_HandSolder | C269434 | R144 | 127.201 | -168.564 | top | 180
1R0 | R145 | Resistor_SMD:R_0603_1608Metric_Pad0.98x0.95mm_HandSolder | C269434 | R145 | 119.581 | -167.548 | top | 90
1R0 | R146 | Resistor_SMD:R_0603_1608Metric_Pad0.98x0.95mm_HandSolder | C269434 | R146 | 123.137 | -168.564 | top | 180
1R0 | R147 | Resistor_SMD:R_0603_1608Metric_Pad0.98x0.95mm_HandSolder | C269434 | R147 | 162.2295 | -46.898 | top | 180
1R0 | R148 | Resistor_SMD:R_0603_1608Metric_Pad0.98x0.95mm_HandSolder | C269434 | R148 | 90.244 | -177.2 | top | 180
1R0 | R149 | Resistor_SMD:R_0603_1608Metric_Pad0.98x0.95mm_HandSolder | C269434 | R149 | 135.837 | -168.056 | top | 180
1R0 | R150 | Resistor_SMD:R_0603_1608Metric_Pad0.98x0.95mm_HandSolder | C269434 | R150 | 105.611 | -167.548 | top | 90
1R0 | R151 | Resistor_SMD:R_0603_1608Metric_Pad0.98x0.95mm_HandSolder | C269434 | R151 | 102.69 | -180.375 | top | 180
1R0 | R152 | Resistor_SMD:R_0603_1608Metric_Pad0.98x0.95mm_HandSolder | C269434 | R152 | 106.119 | -180.375 | top | 0
1R0 | R153 | Resistor_SMD:R_0603_1608Metric_Pad0.98x0.95mm_HandSolder | C269434 | R153 | 109.675 | -180.502 | top | 180
1R0 | R154 | Resistor_SMD:R_0603_1608Metric_Pad0.98x0.95mm_HandSolder | C269434 | R154 | 100.785 | -167.04 | top | 90
1R0 | R155 | Resistor_SMD:R_0603_1608Metric_Pad0.98x0.95mm_HandSolder | C269434 | R155 | 137.361 | -171.104 | top | -90
1R0 | R156 | Resistor_SMD:R_0603_1608Metric_Pad0.98x0.95mm_HandSolder | C269434 | R156 | 103.833 | -167.04 | top | -90
1R0 | R157 | Resistor_SMD:R_0603_1608Metric_Pad0.98x0.95mm_HandSolder | C269434 | R157 | 102.309 | -167.04 | top | -90
1R0 | R158 | Resistor_SMD:R_0603_1608Metric_Pad0.98x0.95mm_HandSolder | C269434 | R158 | 128.471 | -179.994 | top | 180
1R0 | R159 | Resistor_SMD:R_0603_1608Metric_Pad0.98x0.95mm_HandSolder | C269434 | R159 | 122.629 | -179.994 | top | 0
1R0 | R160 | Resistor_SMD:R_0603_1608Metric_Pad0.98x0.95mm_HandSolder | C269434 | R160 | 128.979 | -166.786 | top | 0
1R0 | R161 | Resistor_SMD:R_0603_1608Metric_Pad0.98x0.95mm_HandSolder | C269434 | R161 | 112.723 | -168.31 | top | 180
1R0 | R162 | Resistor_SMD:R_0603_1608Metric_Pad0.98x0.95mm_HandSolder | C269434 | R162 | 162.2295 | -49.692 | top | 180
1R0 | R163 | Resistor_SMD:R_0603_1608Metric_Pad0.98x0.95mm_HandSolder | C269434 | R163 | 162.2295 | -52.486 | top | 180
1R0 | R164 | Resistor_SMD:R_0603_1608Metric_Pad0.98x0.95mm_HandSolder | C269434 | R164 | 162.2295 | -55.534 | top | 180
1R0 | R165 | Resistor_SMD:R_0603_1608Metric_Pad0.98x0.95mm_HandSolder | C269434 | R165 | 72.464 | -162.976 | top | 90
1R0 | R166 | Resistor_SMD:R_0603_1608Metric_Pad0.98x0.95mm_HandSolder | C269434 | R166 | 73.988 | -176.438 | top | 90
4K7 | R167 | Resistor_SMD:R_0603_1608Metric_Pad0.98x0.95mm_HandSolder | C23162 | R167 | 158.4195 | -55.534 | top | 180
4K7 | R168 | Resistor_SMD:R_0603_1608Metric_Pad0.98x0.95mm_HandSolder | C23162 | R168 | 158.57 | -52.486 | top | 180
1R0 | R169 | Resistor_SMD:R_0603_1608Metric_Pad0.98x0.95mm_HandSolder | C269434 | R169 | 163.396 | -191.424 | top | 90
39R | R170 | Resistor_SMD:R_0603_1608Metric_Pad0.98x0.95mm_HandSolder | C325713 | R170 | 162.38 | -108.874 | top | 180
39R | R171 | Resistor_SMD:R_0603_1608Metric_Pad0.98x0.95mm_HandSolder | C325713 | R171 | 162.38 | -106.334 | top | 180
1K | R172 | Resistor_SMD:R_0603_1608Metric_Pad0.98x0.95mm_HandSolder | C269704 | R172 | 162.38 | -92.11 | top | 0
1K | R173 | Resistor_SMD:R_0603_1608Metric_Pad0.98x0.95mm_HandSolder | C269704 | R173 | 156.792 | -151.546 | top | -90
39R | R174 | Resistor_SMD:R_0603_1608Metric_Pad0.98x0.95mm_HandSolder | C325713 | R174 | 162.38 | -87.03 | top | 180
39R | R175 | Resistor_SMD:R_0603_1608Metric_Pad0.98x0.95mm_HandSolder | C325713 | R175 | 162.38 | -84.49 | top | 180
39R | R176 | Resistor_SMD:R_0603_1608Metric_Pad0.98x0.95mm_HandSolder | C325713 | R176 | 162.38 | -81.95 | top | 180
39R | R177 | Resistor_SMD:R_0603_1608Metric_Pad0.98x0.95mm_HandSolder | C325713 | R177 | 152.728 | -151.038 | top | 90
39R | R178 | Resistor_SMD:R_0603_1608Metric_Pad0.98x0.95mm_HandSolder | C325713 | R178 | 154.506 | -151.038 | top | 90
39R | R179 | Resistor_SMD:R_0603_1608Metric_Pad0.98x0.95mm_HandSolder | C325713 | R179 | 150.188 | -150.9345 | top | 90
10K | R180 | Resistor_SMD:R_0603_1608Metric_Pad0.98x0.95mm_HandSolder | C269701 | R180 | 102.055 | -130.287 | top | -90
4K7 | R181 | Resistor_SMD:R_0603_1608Metric_Pad0.98x0.95mm_HandSolder | C23162 | R181 | 102.055 | -134.1705 | top | 90
10K | R182 | Resistor_SMD:R_0603_1608Metric_Pad0.98x0.95mm_HandSolder | C269701 | R182 | 151.839 | -97.698 | top | 0
10K | R183 | Resistor_SMD:R_0603_1608Metric_Pad0.98x0.95mm_HandSolder | C269701 | R183 | 151.839 | -95.158 | top | 0
2K | R184 | Resistor_SMD:R_0603_1608Metric_Pad0.98x0.95mm_HandSolder | C269421 | R184 | 182.827 | -157.388 | top | 180
2K | R185 | Resistor_SMD:R_0603_1608Metric_Pad0.98x0.95mm_HandSolder | C269421 | R185 | 181.811 | -84.49 | top | 180
1K | R201 | Resistor_SMD:R_0603_1608Metric_Pad0.98x0.95mm_HandSolder | C269704 | R201 | 211.275 | -200.1635 | top | -90
1K | R202 | Resistor_SMD:R_0603_1608Metric_Pad0.98x0.95mm_HandSolder | C269704 | R202 | 208.511 | -200.1635 | top | -90
1K | R203 | Resistor_SMD:R_0603_1608Metric_Pad0.98x0.95mm_HandSolder | C269704 | R203 | 205.687 | -200.1635 | top | -90
1K | R204 | Resistor_SMD:R_0603_1608Metric_Pad0.98x0.95mm_HandSolder | C269704 | R204 | 202.893 | -200.1635 | top | -90
1R0 | R801 | Resistor_SMD:R_0603_1608Metric_Pad0.98x0.95mm_HandSolder | C269434 | R801 | 90.7285 | -175.168 | top | 0
10K | R802 | Resistor_SMD:R_0603_1608Metric_Pad0.98x0.95mm_HandSolder | C269701 | R802 | 191.209 | -193.8135 | top | 90
1K | R803 | Resistor_SMD:R_0603_1608Metric_Pad0.98x0.95mm_HandSolder | C269704 | R803 | 194.003 | -194.98 | top | 0
1R0 | R804 | Resistor_SMD:R_0603_1608Metric_Pad0.98x0.95mm_HandSolder | C269434 | R804 | 194.765 | -164.53 | top | 0
1R0 | R806 | Resistor_SMD:R_0603_1608Metric_Pad0.98x0.95mm_HandSolder | C269434 | R806 | 198.6785 | -190.916 | top | 0
1R0 | R807 | Resistor_SMD:R_0603_1608Metric_Pad0.98x0.95mm_HandSolder | C269434 | R807 | 194.765 | -169.072 | top | 180
SWITCH_TACTILE_SPST-NO_0.05A_24V | S1 | PubInv_KiCad_PCB:Switch_Tactile_THT_6x6mm | C428628 | S1 | 88.75 | -52.75 | top | 0
SWITCH_TACTILE_SPST-NO_0.05A_24V | S2 | PubInv_KiCad_PCB:Switch_Tactile_THT_6x6mm | C428628 | S2 | 68 | -219.75 | top | 180
GND | TP1 | TestPoint:TestPoint_Loop_D2.54mm_Drill1.5mm_Beaded | C7589090 | TP1 | 55 | -196.75 | top | 0
+12V | TP2 | TestPoint:TestPoint_Loop_D2.54mm_Drill1.5mm_Beaded | C5277086 | TP2 | 103.25 | -61 | top | 90
GND | TP3 | TestPoint:TestPoint_Loop_D2.54mm_Drill1.5mm_Beaded | C7589090 | TP3 | 103 | -65 | top | 0
GND | TP4 | TestPoint:TestPoint_Loop_D2.54mm_Drill1.5mm_Beaded | C7589090 | TP4 | 60.5 | -60 | top | 0
+VccMAX31850 | TP5 | TestPoint:TestPoint_Loop_D2.54mm_Drill1.5mm_Beaded | C5277086 | TP5 | 161.237 | -217.332 | top | 180
+VccMAX31850_1 | TP6 | TestPoint:TestPoint_Loop_D2.54mm_Drill1.5mm_Beaded | C5277086 | TP6 | 141 | -188.95 | top | 180
+VccMAX31850_2 | TP7 | TestPoint:TestPoint_Loop_D2.54mm_Drill1.5mm_Beaded | C5277086 | TP7 | 114.5 | -188.95 | top | 180
+VccMAX31850_3 | TP8 | TestPoint:TestPoint_Loop_D2.54mm_Drill1.5mm_Beaded | C5277086 | TP8 | 86 | -188.95 | top | 180
+VccMAX3185 | TP9 | TestPoint:TestPoint_Loop_D2.54mm_Drill1.5mm_Beaded | C5277086 | TP9 | 163 | -211.45 | top | 180
+VccMCP9600 | TP10 | TestPoint:TestPoint_Loop_D2.54mm_Drill1.5mm_Beaded | C5277086 | TP10 | 163 | -205.75 | top | 180
GND | TP11 | TestPoint:TestPoint_Loop_D2.54mm_Drill1.5mm_Beaded | C7589090 | TP11 | 53 | -120.5 | top | 0
I2C_VCC | TP17 | TestPoint:TestPoint_Loop_D2.54mm_Drill1.5mm_Beaded | C5277086 | TP17 | 63 | -163 | top | 90
SCL_5V | TP18 | TestPoint:TestPoint_Loop_D2.54mm_Drill1.5mm_Beaded | C5277086 | TP18 | 63.5 | -188 | top | 90
SDA_5V | TP19 | TestPoint:TestPoint_Loop_D2.54mm_Drill1.5mm_Beaded | C5277086 | TP19 | 68.5 | -163 | top | 0
+24V | TP20 | TestPoint:TestPoint_Loop_D2.54mm_Drill1.5mm_Beaded | C5277086 | TP20 | 64.5 | -54.75 | top | 0
GND | TP21 | TestPoint:TestPoint_Loop_D2.54mm_Drill1.5mm_Beaded | C7589090 | TP21 | 184.859 | -46.644 | top | 0
+VccMAX31850_3 | TP201 | TestPoint:TestPoint_Loop_D2.54mm_Drill1.5mm_Beaded | C5277086 | TP201 | 199.845 | -200.06 | top | 180
Switched_Fan_Power | TPSwitched_Fan_Power1 | TestPoint:TestPoint_Loop_D2.54mm_Drill1.5mm_Beaded | C5277086 | TPSwitched_Fan_Power1 | 58 | -120.5 | top | 0
CIPO | TP_CIPO1 | TestPoint:TestPoint_Loop_D2.54mm_Drill1.5mm_Beaded | C5199804 | TP_CIPO1 | 92.022 | -149.514 | top | 0
COPI | TP_COPI1 | TestPoint:TestPoint_Loop_D2.54mm_Drill1.5mm_Beaded | C5199804 | TP_COPI1 | 89.863 | -171.358 | top | 0
SCL | TP_SCL1 | TestPoint:TestPoint_Loop_D2.54mm_Drill1.5mm_Beaded | C5199804 | TP_SCL1 | 149.045 | -164.5 | top | 0
SCL1 | TP_SCL2 | TestPoint:TestPoint_Loop_D2.54mm_Drill1.5mm_Beaded | C5199804 | TP_SCL2 | 170.254 | -47.66 | top | 0
SDA | TP_SDA1 | TestPoint:TestPoint_Loop_D2.54mm_Drill1.5mm_Beaded | C5199804 | TP_SDA1 | 157.3 | -165.77 | top | 0
SDA1 | TP_SDA2 | TestPoint:TestPoint_Loop_D2.54mm_Drill1.5mm_Beaded | C5199804 | TP_SDA2 | 165.682 | -59.344 | top | 0
TP_SD_DET | TP_SD_DET1 | TestPoint:TestPoint_Loop_D2.54mm_Drill1.5mm_Beaded | C5199804 | TP_SD_DET1 | 97.991 | -166.532 | top | 0
SPI_SCK | TP_SPI_SCK1 | TestPoint:TestPoint_Loop_D2.54mm_Drill1.5mm_Beaded | C5199804 | TP_SPI_SCK1 | 85.291 | -170.342 | top | 0
VIN1 | TP_VIN1 | TestPoint:TestPoint_Loop_D2.54mm_Drill1.5mm_Beaded | C5277086 | TP_VIN1 | 97.61 | -64.932 | top | 0
