LokiMetaSmith/NASA-COG/elec/Control Board/Control_1v1/MountMini12864/MountMini12864 - Facebook20231209.FCStd

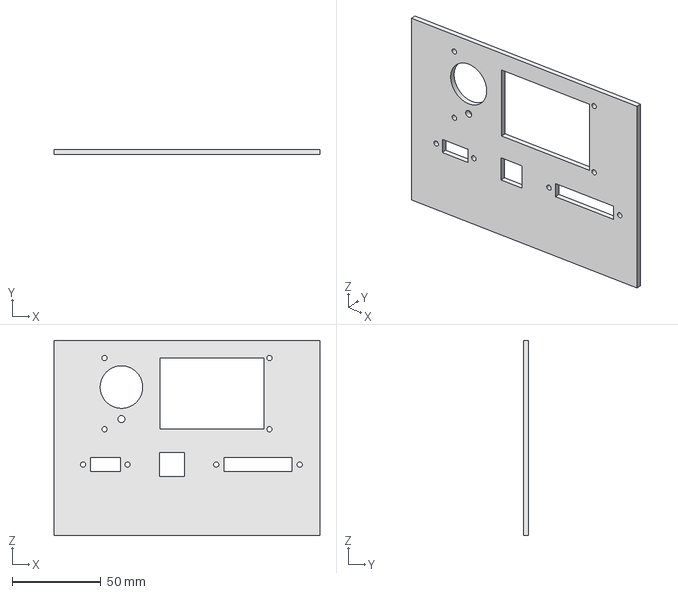
[picture p25: CAD file, 2024-07-01]
elec/Control Board/Control_1v1/MountMini12864/MountMini12864 - Facebook20231209.FCStd
150.0 x 3.00 x 110.0 mm
