LokiMetaSmith/NASA-COG/elec/Control Board/Control_1v2/PublicInvention_KiCad_Library/Parts/rj11-connectors-6p-1.snapshot.1/Amphenol_54601_RT_ANGLE.step

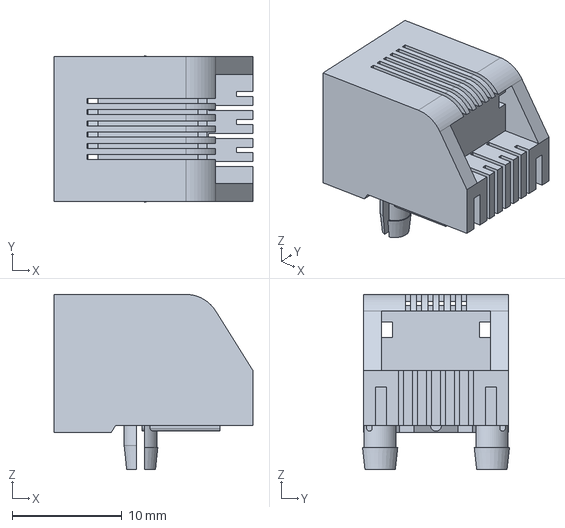
[picture p27: CAD file, 2024-12-05]
elec/Control Board/Control_1v2/PublicInvention_KiCad_Library/Parts/rj11-connectors-6p-1.snapshot.1/Amphenol_54601_RT_ANGLE.step
18.1 x 13.4 x 15.9 mm
