LokiMetaSmith/NASA-COG/elec/Control Board/Control_1v2/PublicInvention_KiCad_Library/Parts/TS6-THT-SQ.step

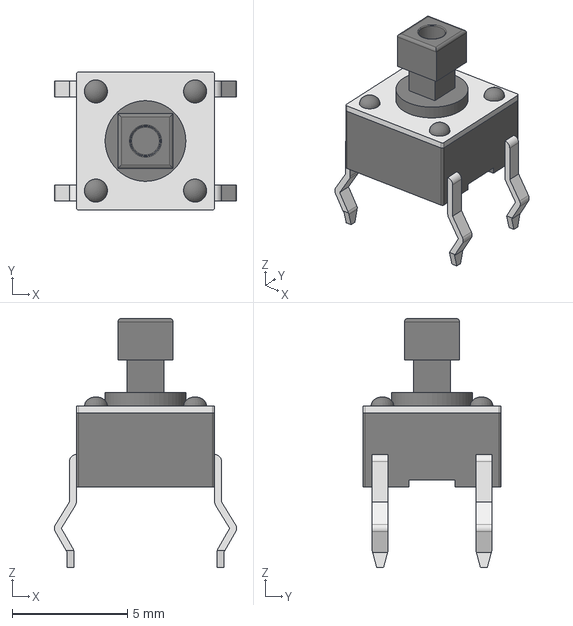
[picture p28: CAD file, 2024-12-05]
elec/Control Board/Control_1v2/PublicInvention_KiCad_Library/Parts/TS6-THT-SQ.step
7.90 x 6.00 x 10.8 mm
