LokiMetaSmith/NASA-COG/elec/Control Board/Control_1v2/PublicInvention_KiCad_Library/Parts/2004A_ap214.STEP

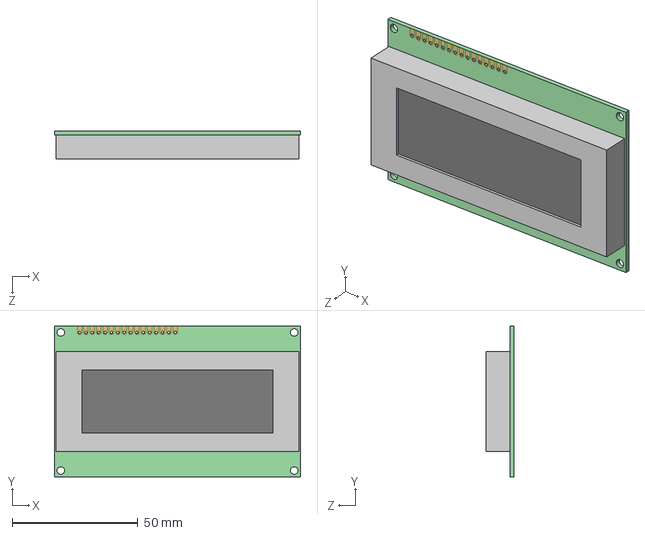
[picture p29: CAD file, 2024-12-05]
elec/Control Board/Control_1v2/PublicInvention_KiCad_Library/Parts/2004A_ap214.STEP
98.0 x 60.0 x 11.1 mm
