LokiMetaSmith/NASA-COG/elec/Control Board/Control_1v2/PublicInvention_KiCad_Library/Parts/BarrelJackSMD v3.step

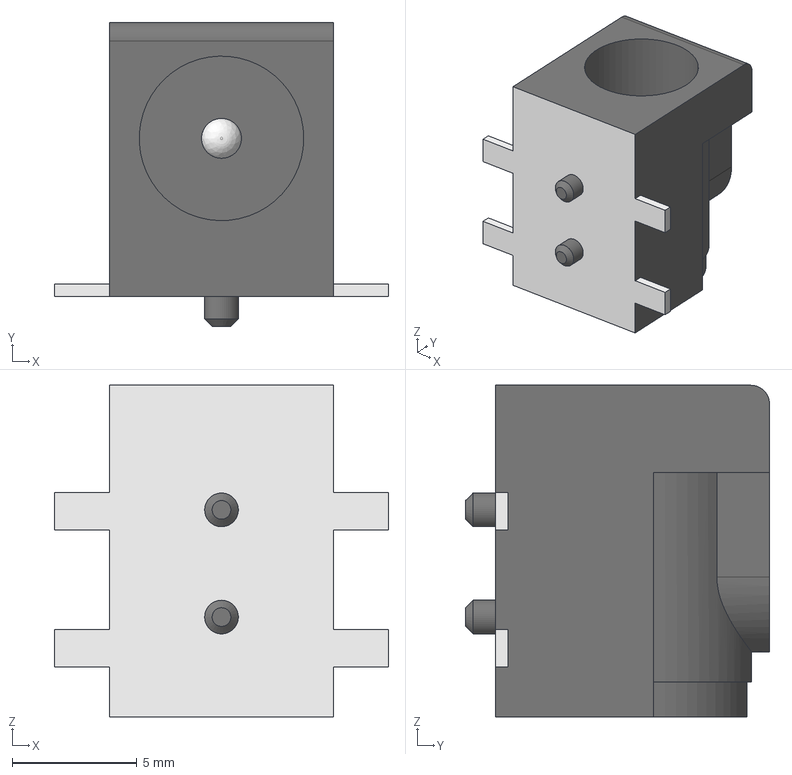
[picture p30: CAD file, 2024-12-05]
elec/Control Board/Control_1v2/PublicInvention_KiCad_Library/Parts/BarrelJackSMD v3.step
13.4 x 12.2 x 13.3 mm
