LokiMetaSmith/NASA-COG/elec/Control Board/Control_1v2/PublicInvention_KiCad_Library/Parts/LED 5MM TH WHITE.STEP

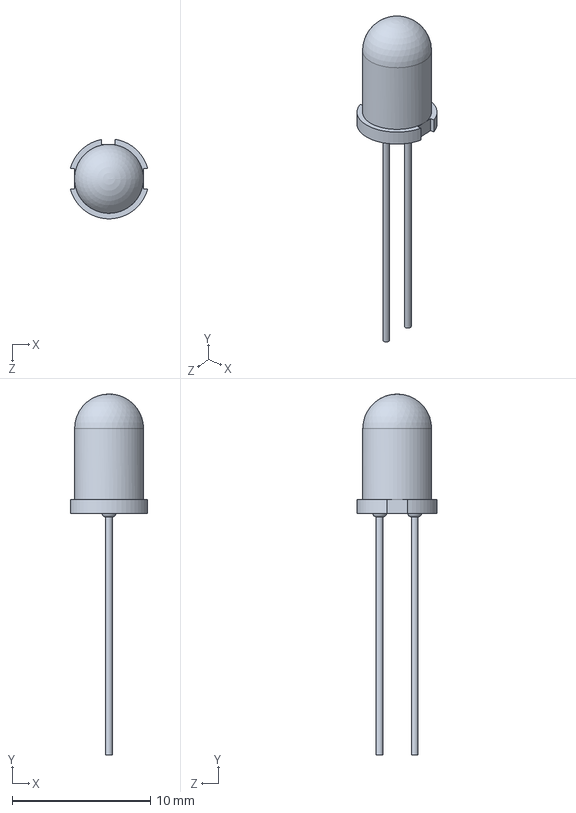
[picture p32: CAD file, 2024-12-05]
elec/Control Board/Control_1v2/PublicInvention_KiCad_Library/Parts/LED 5MM TH WHITE.STEP
5.60 x 26.1 x 5.76 mm
