LokiMetaSmith/NASA-COG/elec/Control Board/Control_1v2/PublicInvention_KiCad_Library/Parts/10K,  BOURNS 3362P-103LF.STEP

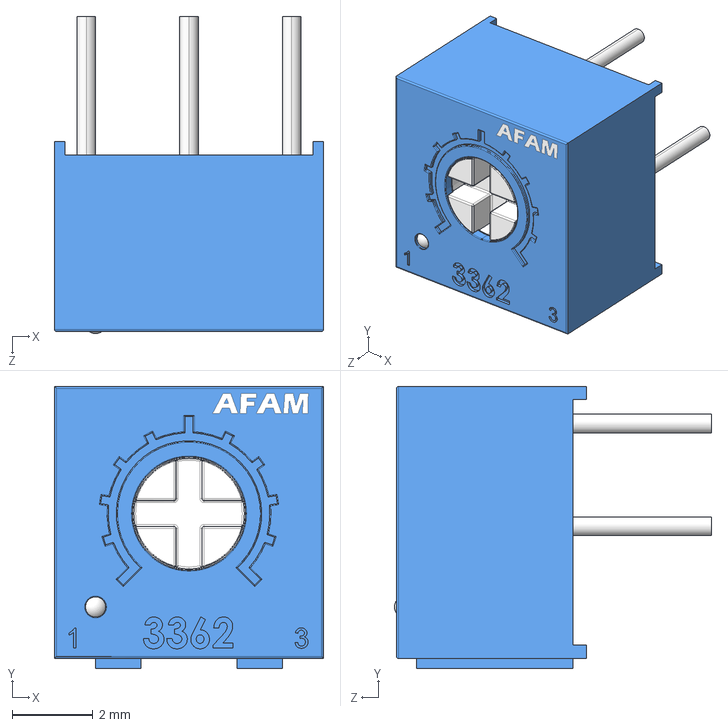
[picture p33: CAD file, 2024-12-05]
elec/Control Board/Control_1v2/PublicInvention_KiCad_Library/Parts/10K, BOURNS 3362P-103LF.STEP
6.66 x 6.99 x 7.85 mm
