LokiMetaSmith/NASA-COG/elec/Control Board/Control_1v1/FabricationPhotos/20231027_171457.jpg

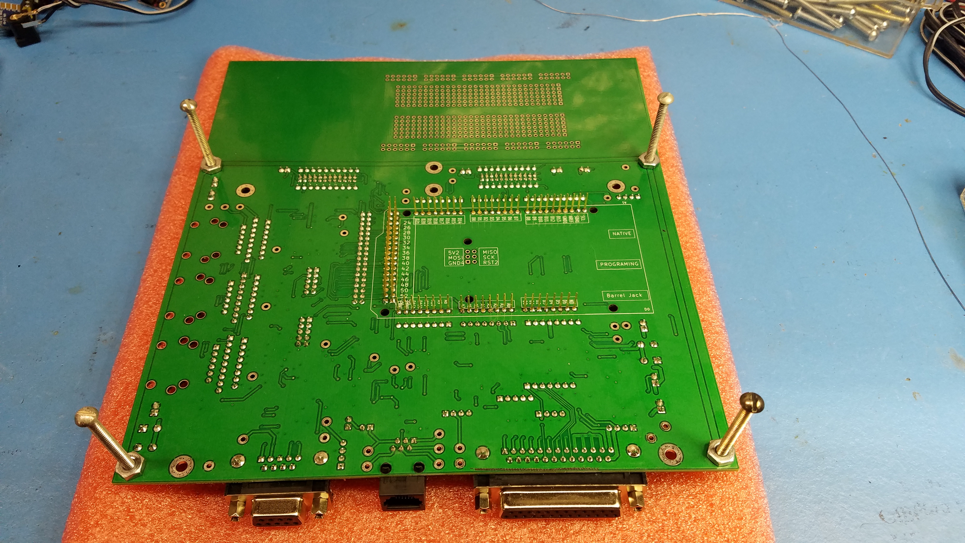
elec/Control Board/Control_1v1/FabricationPhotos/20231027_171457.jpg
