LokiMetaSmith/NASA-COG/elec/Control Board/Control_1v1/FabricationPhotos/PXL_20240129_171221279.jpg

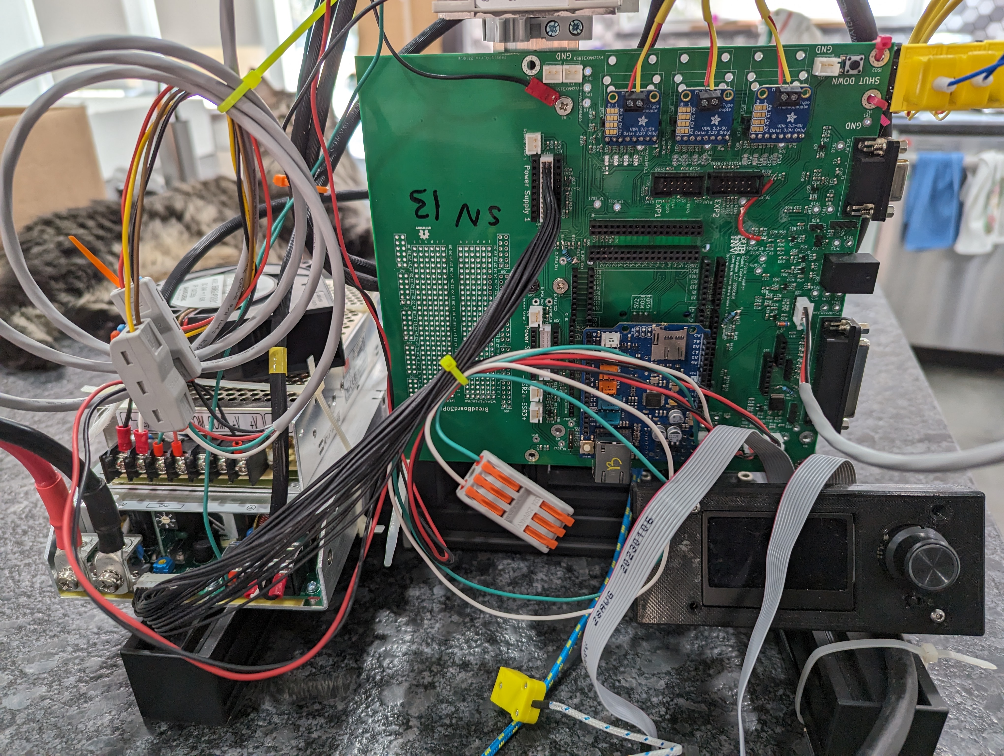
elec/Control Board/Control_1v1/FabricationPhotos/PXL_20240129_171221279.jpg
