LokiMetaSmith/NASA-COG/elec/Control Board/Control_1v1/FabricationPhotos/ReworkFor5VUARTto3V3.jpg

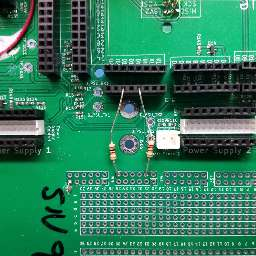
elec/Control Board/Control_1v1/FabricationPhotos/ReworkFor5VUARTto3V3.jpg
