LokiMetaSmith/NASA-COG/elec/Control Board/Control_1v1/FabricationPhotos/SN11_SPAM_b.jpg

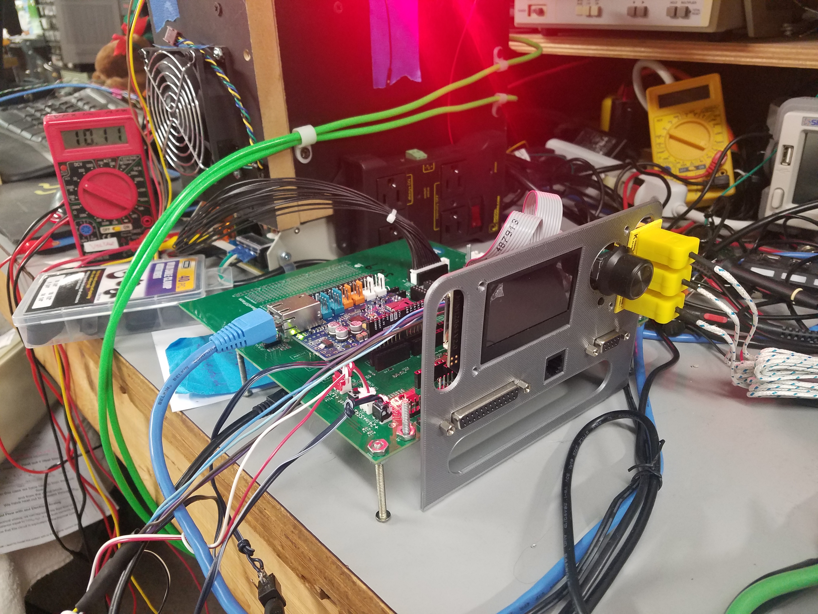
elec/Control Board/Control_1v1/FabricationPhotos/SN11_SPAM_b.jpg
