LokiMetaSmith/NASA-COG/elec/Control Board/Control_1v1/FabricationPhotos/SPAM_Annotatedb.jpg

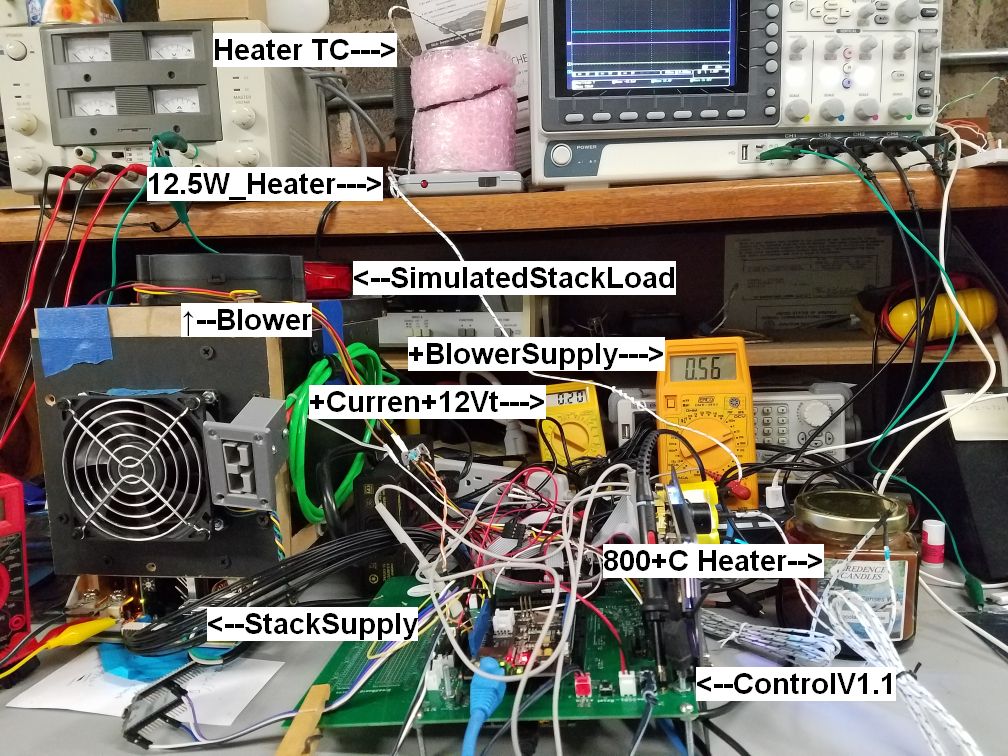
elec/Control Board/Control_1v1/FabricationPhotos/SPAM_Annotatedb.jpg
