LokiMetaSmith/NASA-COG/elec/Control Board/Control_1v1/FabricationPhotos/ThermoCoupleAmp_20231117_172323.jpg

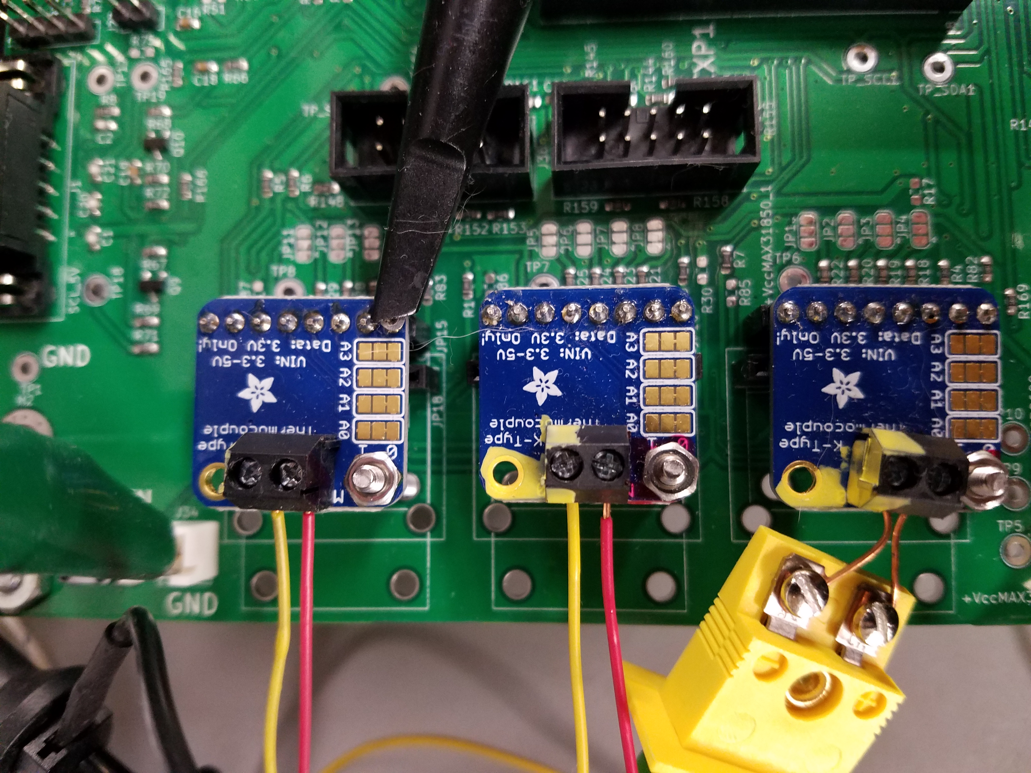
elec/Control Board/Control_1v1/FabricationPhotos/ThermoCoupleAmp_20231117_172323.jpg
