LokiMetaSmith/NASA-COG/elec/Control Board/Control_1v1/FabricationPhotos/SN11_FactoryTest_c.jpg

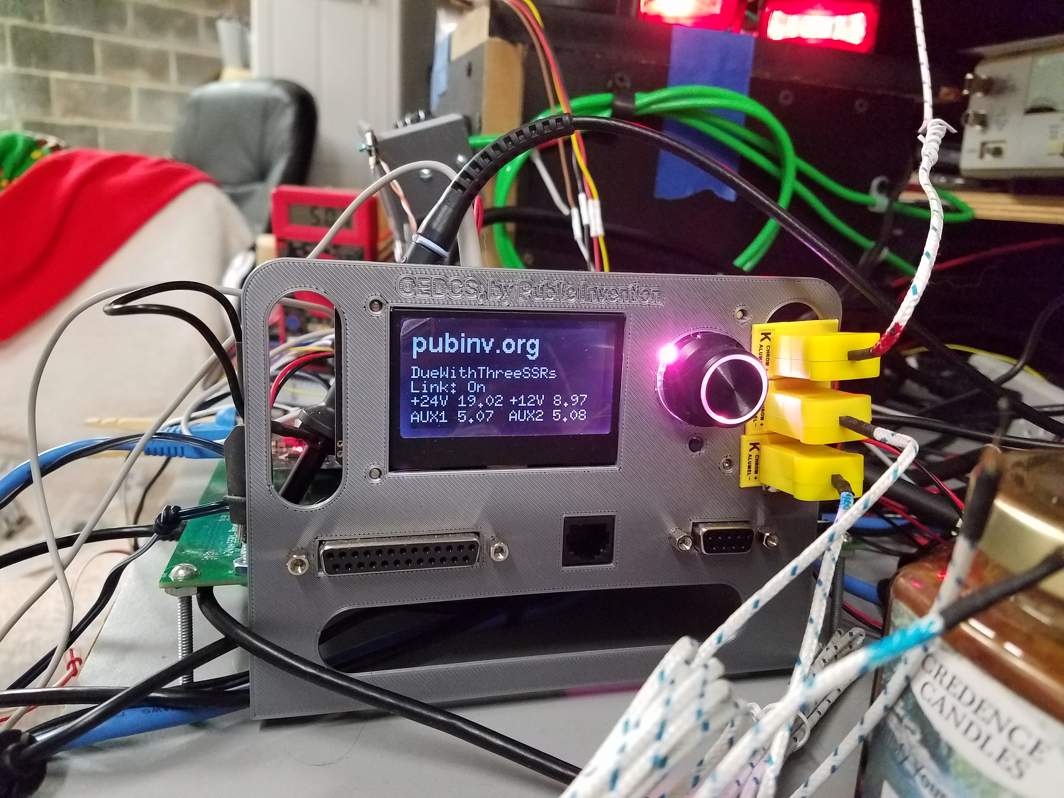
elec/Control Board/Control_1v1/FabricationPhotos/SN11_FactoryTest_c.jpg
