LokiMetaSmith/NASA-COG/firmware-development/experimentation/EventUARTS_Due/RuntPulseAfteReset.png

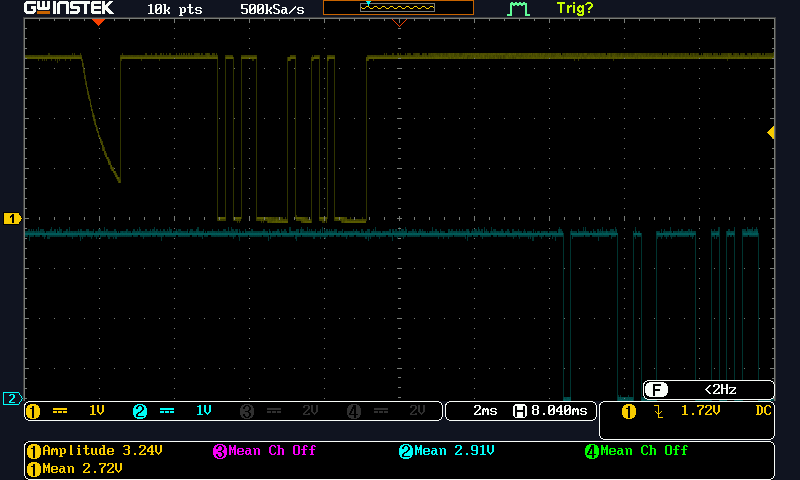
firmware-development/experimentation/EventUARTS_Due/RuntPulseAfteReset.png
