LokiMetaSmith/NASA-COG/firmware-development/experimentation/EventUARTS_Due/TX_DEVI_succsfull.png

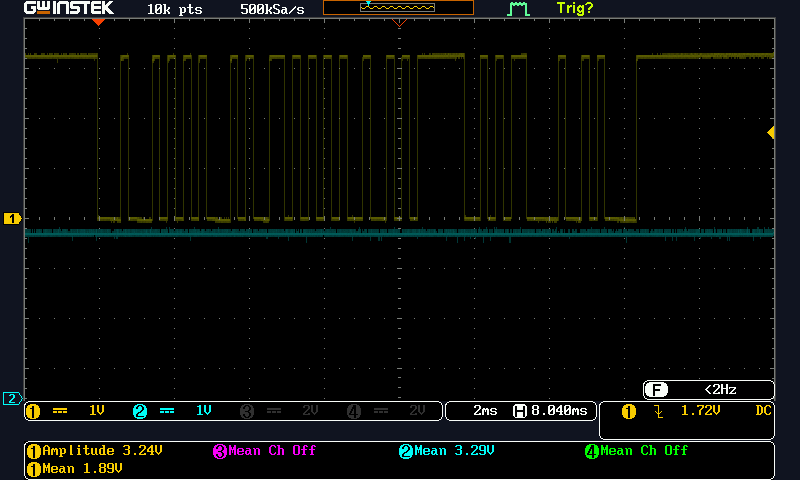
firmware-development/experimentation/EventUARTS_Due/TX_DEVI_succsfull.png
