LokiMetaSmith/NASA-COG/elec/Control Board/Control_1v1/MountMini12864/MountMini12864_20231205_a.pdf

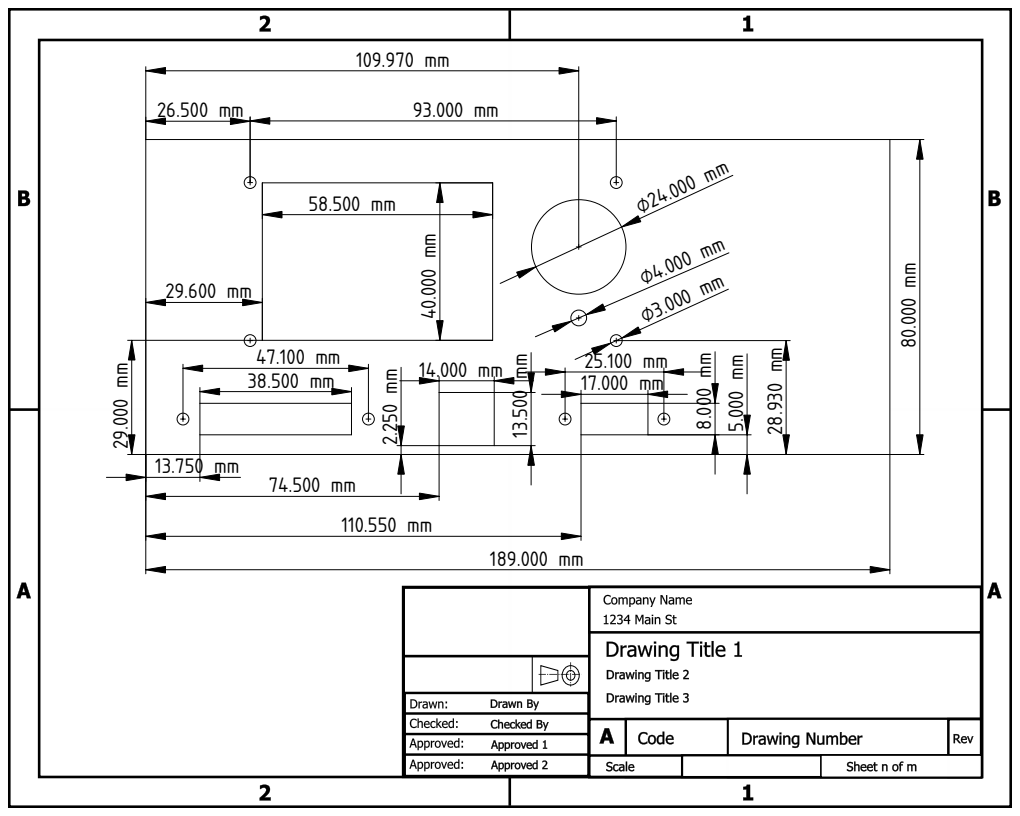
[picture p70: page 1]
