LokiMetaSmith/NASA-COG/elec/Control Board/Control_1v1/FabricationPhotos/20231026_184748.jpg

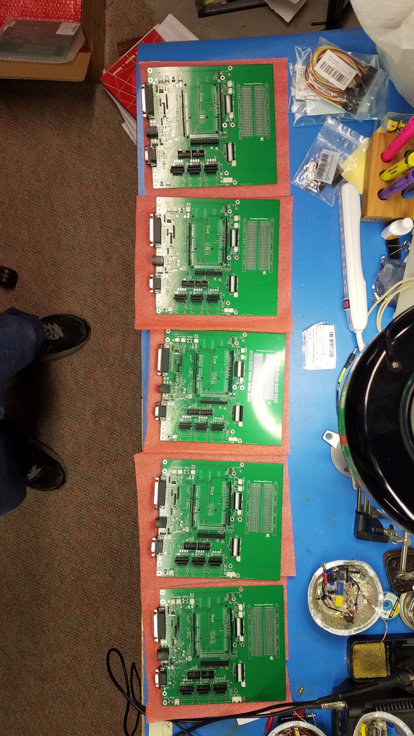
elec/Control Board/Control_1v1/FabricationPhotos/20231026_184748.jpg
