LokiMetaSmith/NASA-COG/elec/Control Board/Control_1v1/FabricationPhotos/Rework20231209_181516.jpg

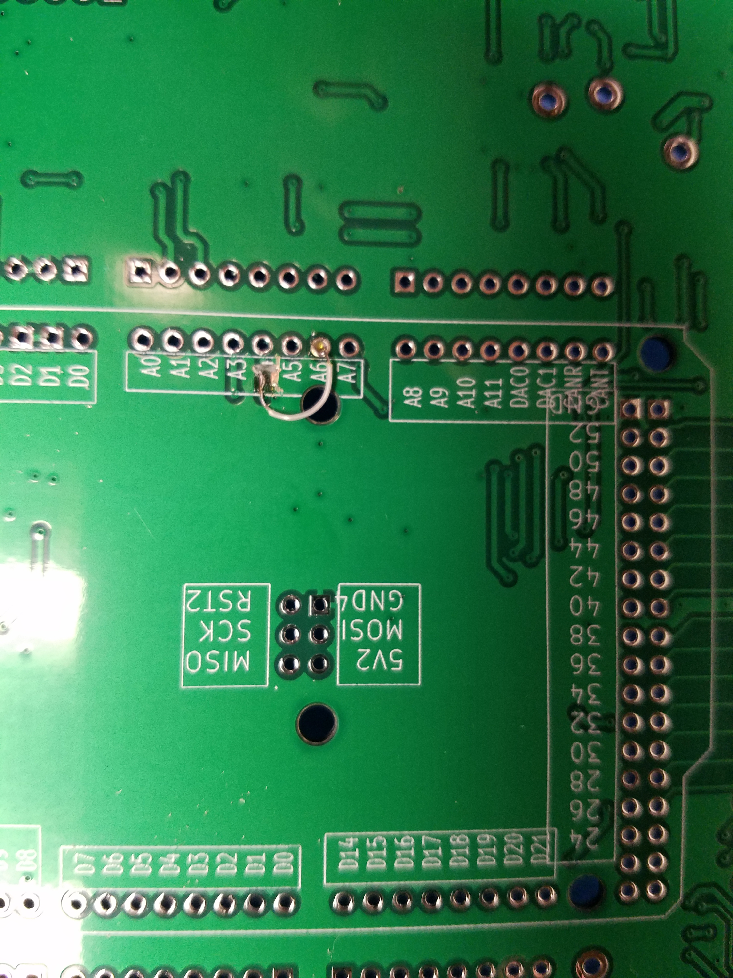
elec/Control Board/Control_1v1/FabricationPhotos/Rework20231209_181516.jpg
