LokiMetaSmith/NASA-COG/elec/Control Board/Control_1v2/Manufacturing_Files/FabricationPhotos/20250130_075907.jpg

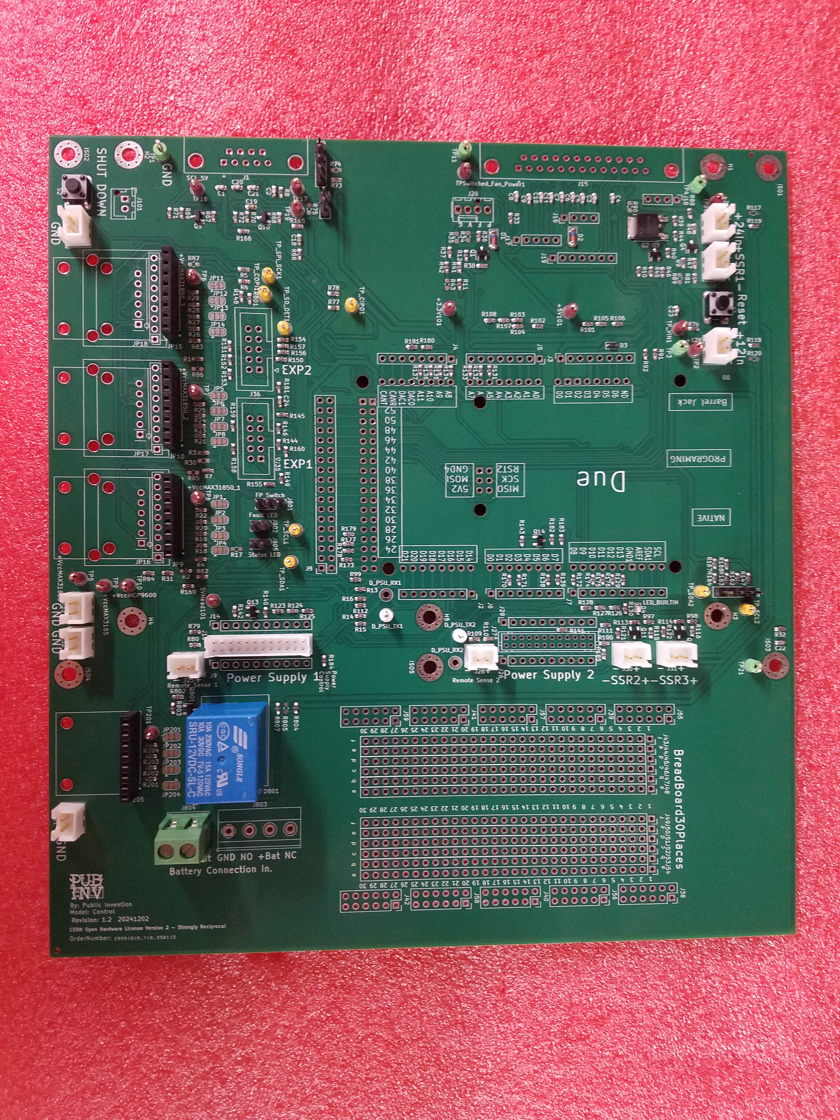
elec/Control Board/Control_1v2/Manufacturing_Files/FabricationPhotos/20250130_075907.jpg
